bkw777/NODE_DATAPAC/PCB/out/MiniNDP_1M_B.bottom.jpg

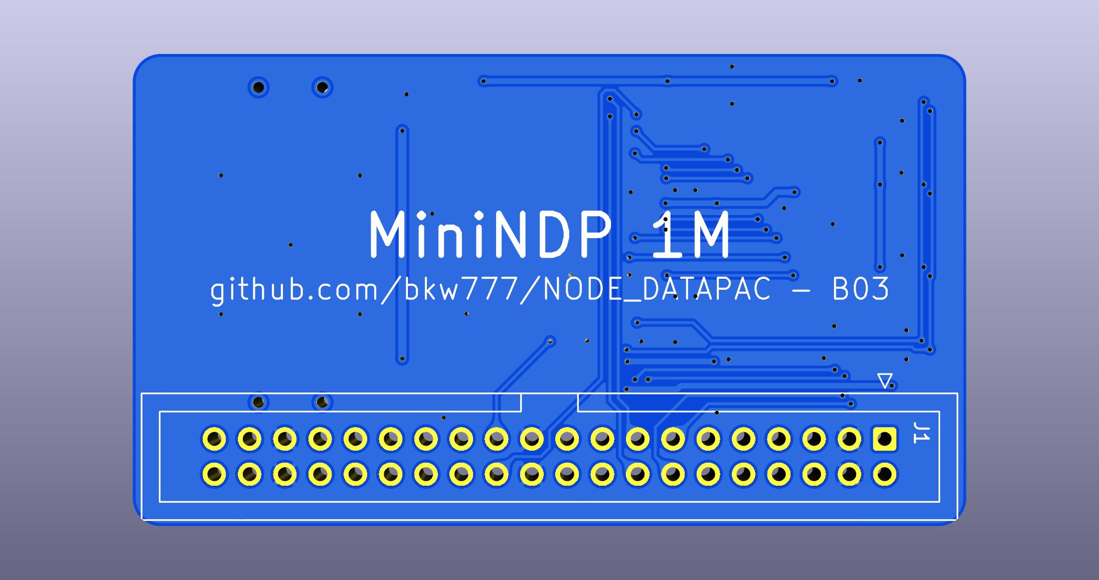
PCB/out/MiniNDP_1M_B.bottom.jpg
