bkw777/NODE_DATAPAC/PCB/out/MiniNDP_1M_B.top.jpg

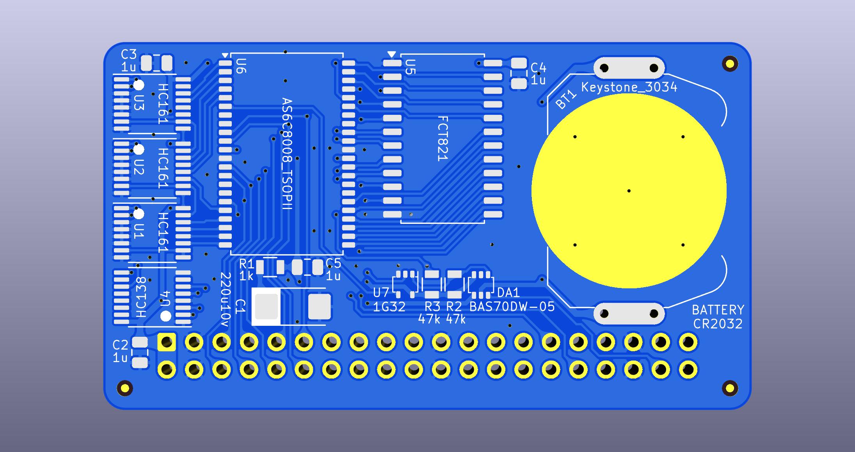
PCB/out/MiniNDP_1M_B.top.jpg
