bkw777/NODE_DATAPAC/PCB/out/MiniNDP_256_CR2016.jpg

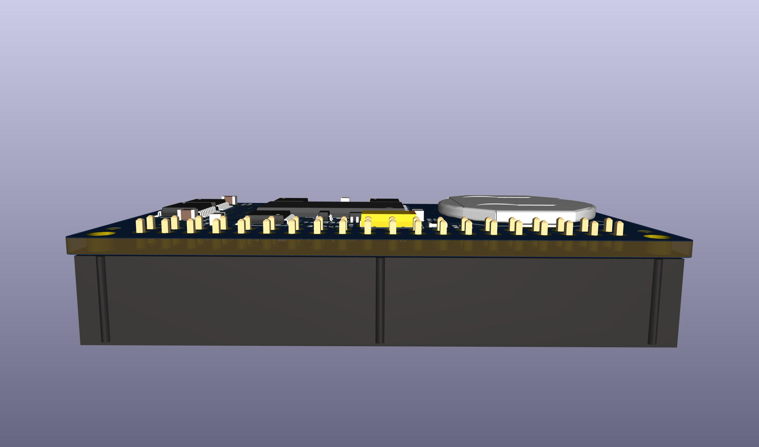
PCB/out/MiniNDP_256_CR2016.jpg
