bkw777/NODE_DATAPAC/PCB/out/MiniNDP_OG.bottom.jpg

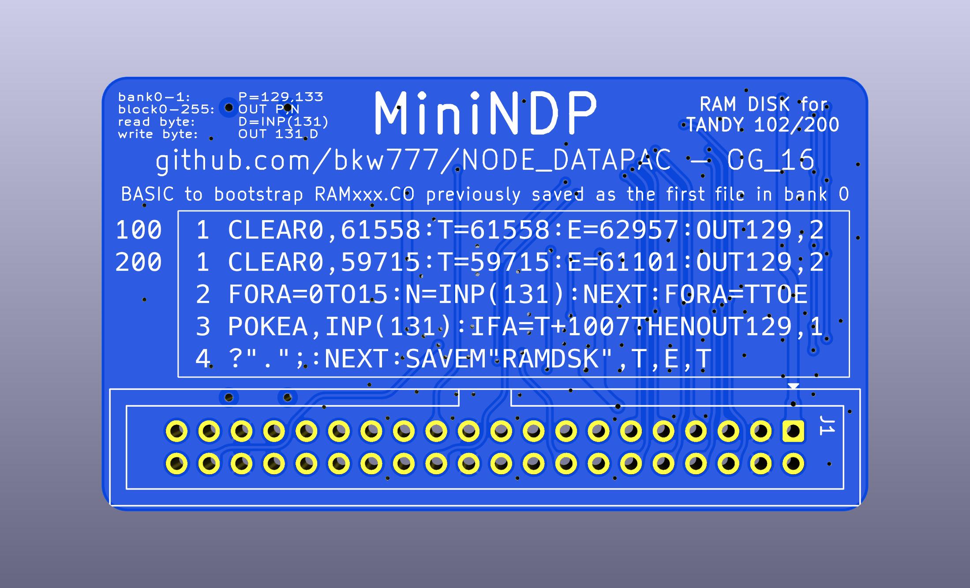
PCB/out/MiniNDP_OG.bottom.jpg
