bkw777/NODE_DATAPAC/PCB/out/MiniNDP_OG.jpg

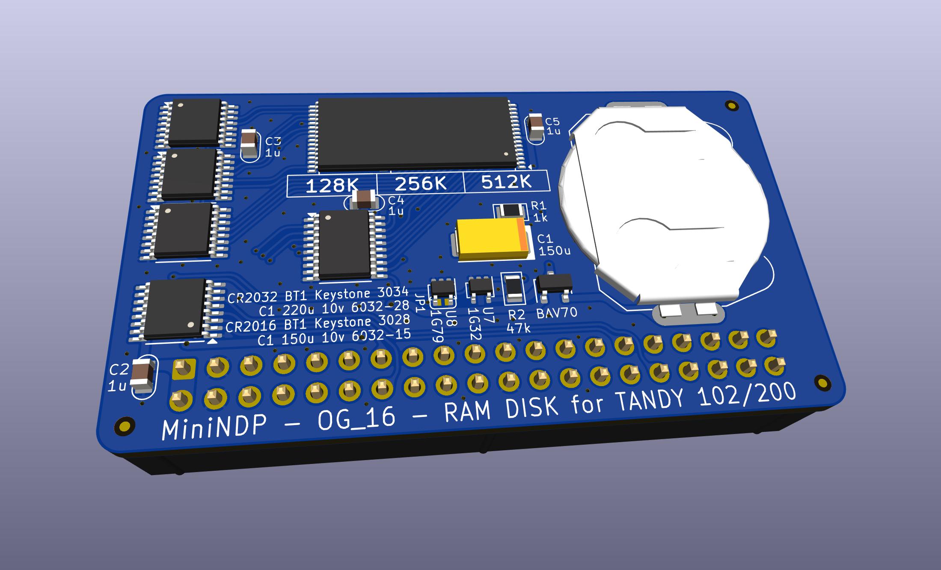
PCB/out/MiniNDP_OG.jpg
