bkw777/NODE_DATAPAC/PCB/out/MiniNDP_OG.top.jpg

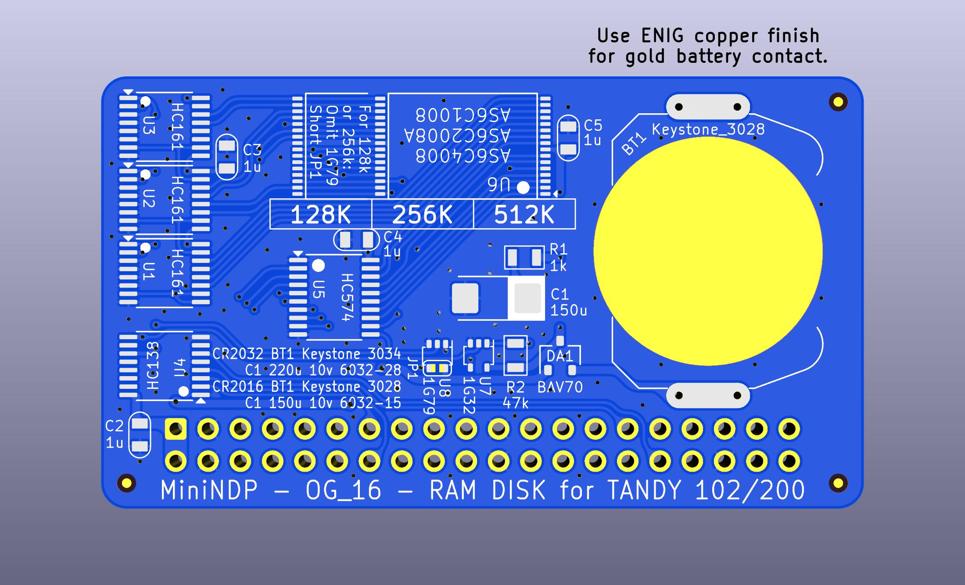
PCB/out/MiniNDP_OG.top.jpg
