bkw777/NODE_DATAPAC/PCB/out/NODE_DATAPAC_256K_bkw.bottom.jpg

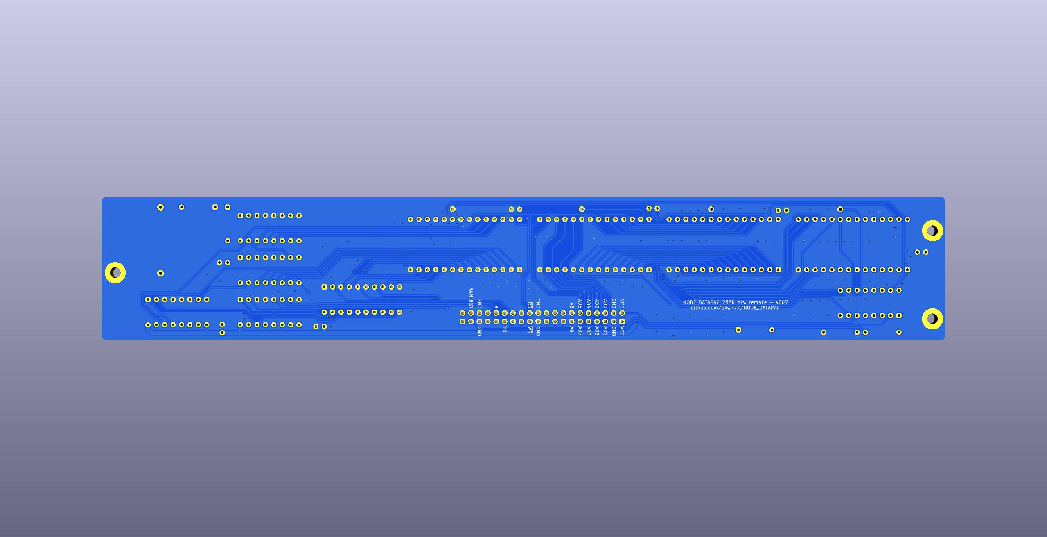
PCB/out/NODE_DATAPAC_256K_bkw.bottom.jpg
