bkw777/NODE_DATAPAC/PCB/out/NODE_DATAPAC_256K_bkw.f.jpg

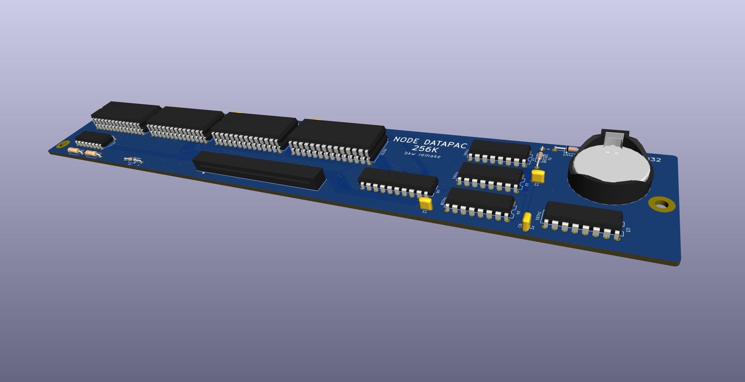
PCB/out/NODE_DATAPAC_256K_bkw.f.jpg
