bkw777/NODE_DATAPAC/PCB/out/NODE_DATAPAC_256K_historical_reproduction_2.jpg

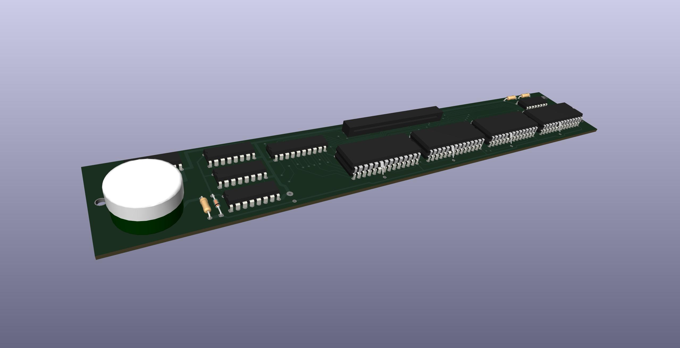
PCB/out/NODE_DATAPAC_256K_historical_reproduction_2.jpg
