bkw777/NODE_DATAPAC/PICS/cover_1.jpg

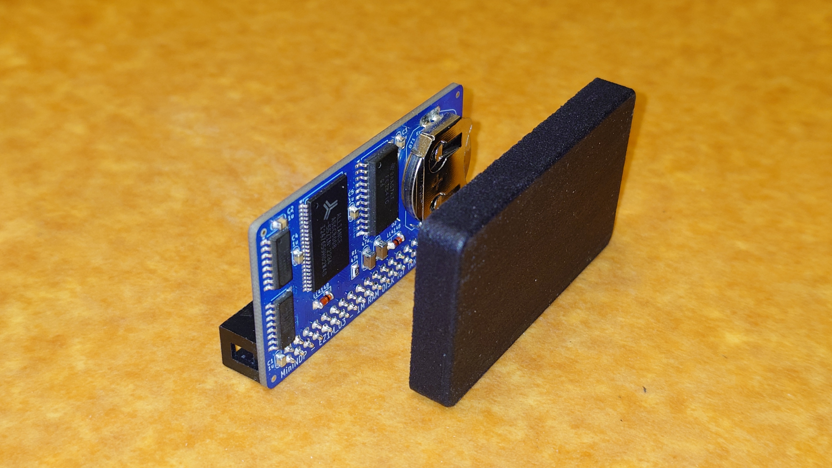
PICS/cover_1.jpg
