bkw777/NODE_DATAPAC/PICS/cover_2.jpg

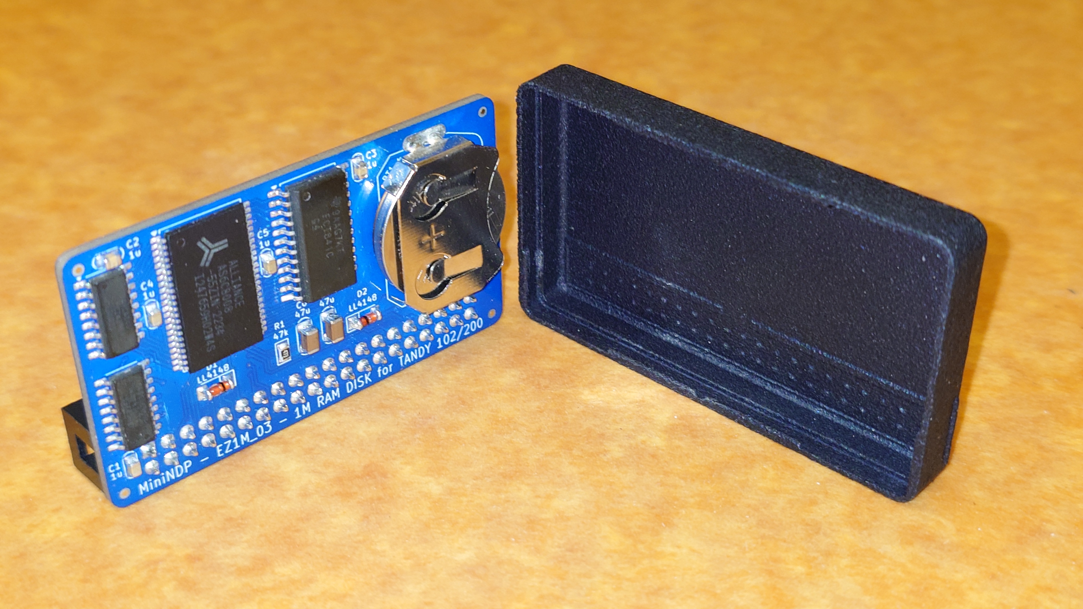
PICS/cover_2.jpg
