bkw777/NODE_DATAPAC/PICS/cover_3.jpg

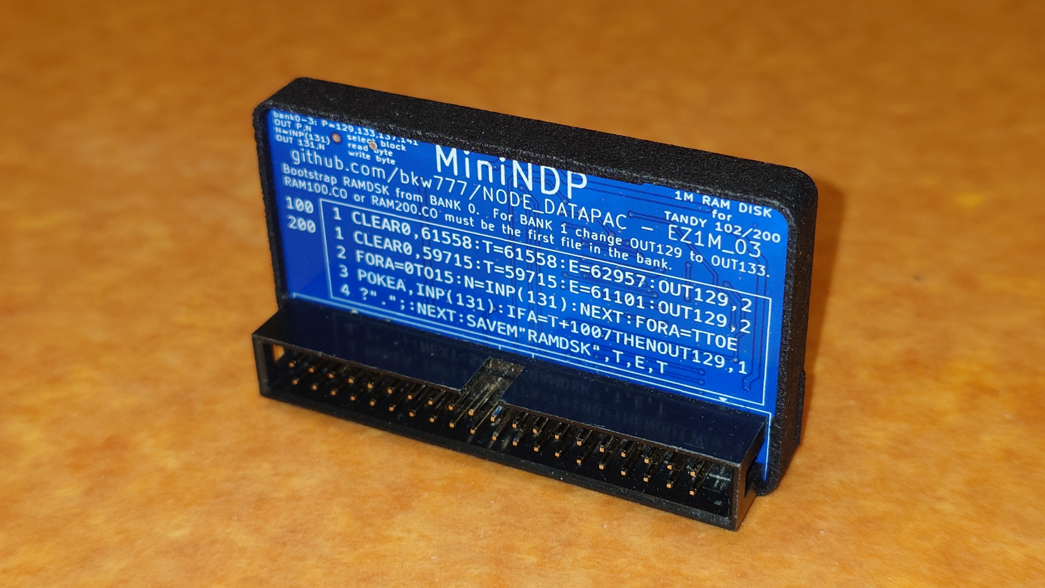
PICS/cover_3.jpg
