bkw777/NODE_DATAPAC/PICS/cover_102.jpg

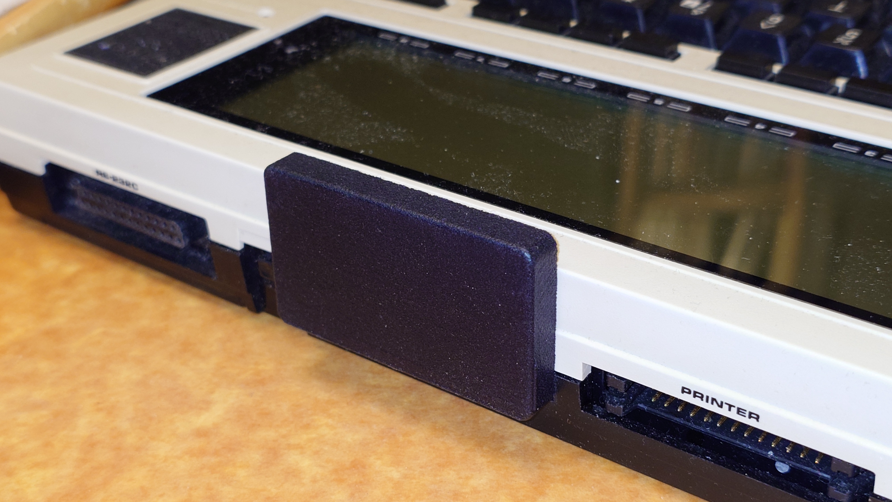
PICS/cover_102.jpg
