bkw777/NODE_DATAPAC/PICS/cover_200.jpg

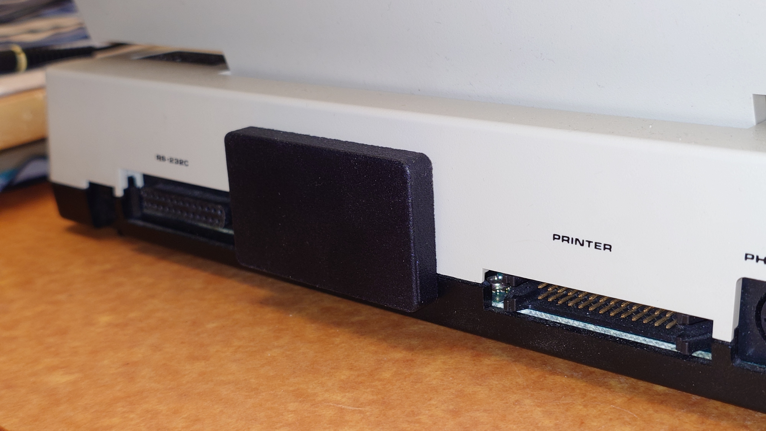
PICS/cover_200.jpg
