bkw777/NODE_DATAPAC/PICS/Cover_thin.1.jpg

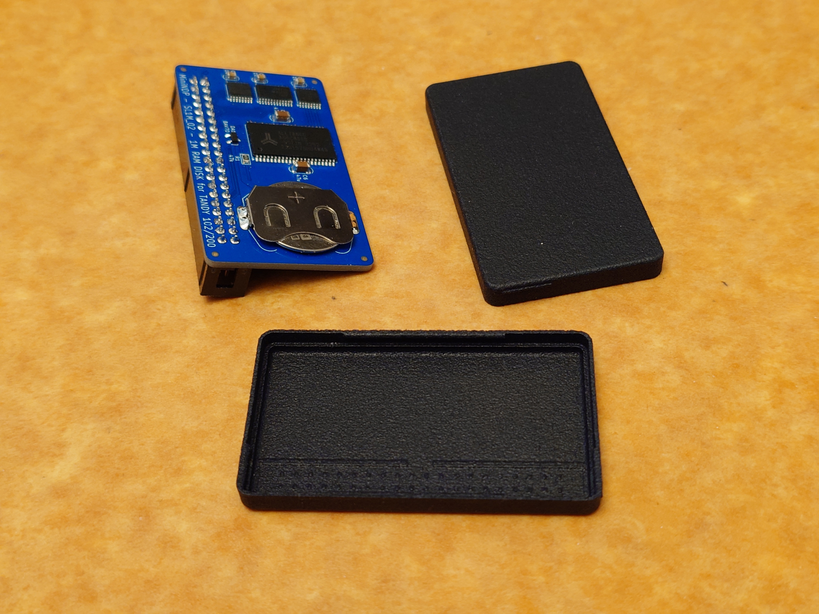
PICS/Cover_thin.1.jpg
