bkw777/NODE_DATAPAC/PICS/Cover_thin.2.jpg

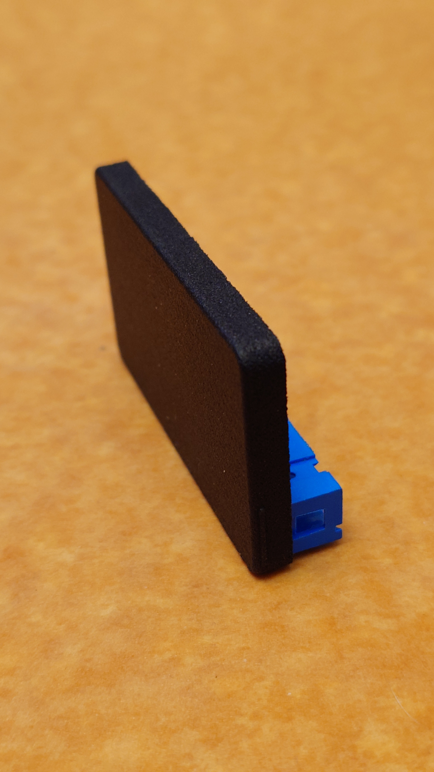
PICS/Cover_thin.2.jpg
