bkw777/NODE_DATAPAC/PICS/DATAPAC/549330443_10163459711251760_8373819885439464849_n.jpg

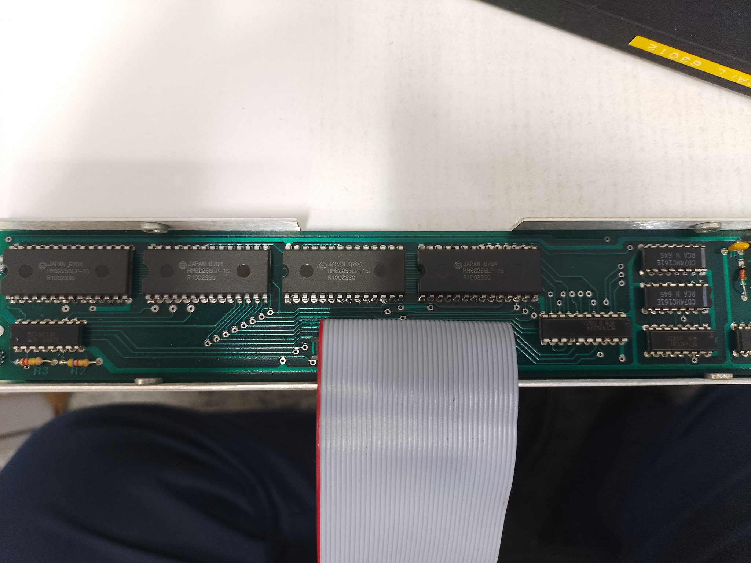
PICS/DATAPAC/549330443_10163459711251760_8373819885439464849_n.jpg
