bkw777/NODE_DATAPAC/PICS/DATAPAC/552761636_10163459711391760_1145795438437594282_n.jpg

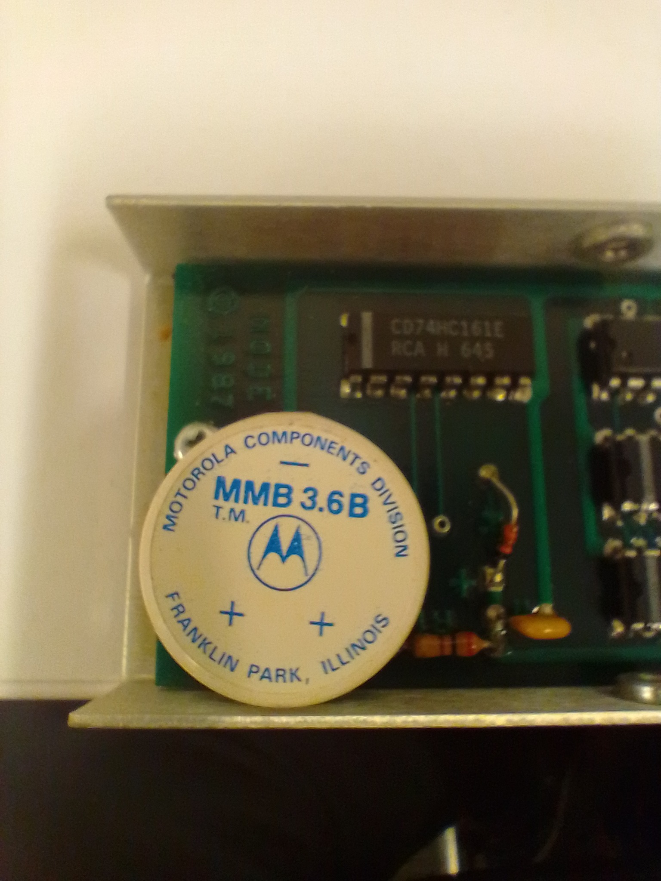
PICS/DATAPAC/552761636_10163459711391760_1145795438437594282_n.jpg
