bkw777/NODE_DATAPAC/PICS/DATAPAC/553972267_10163459710006760_2879506041436889275_n.jpg

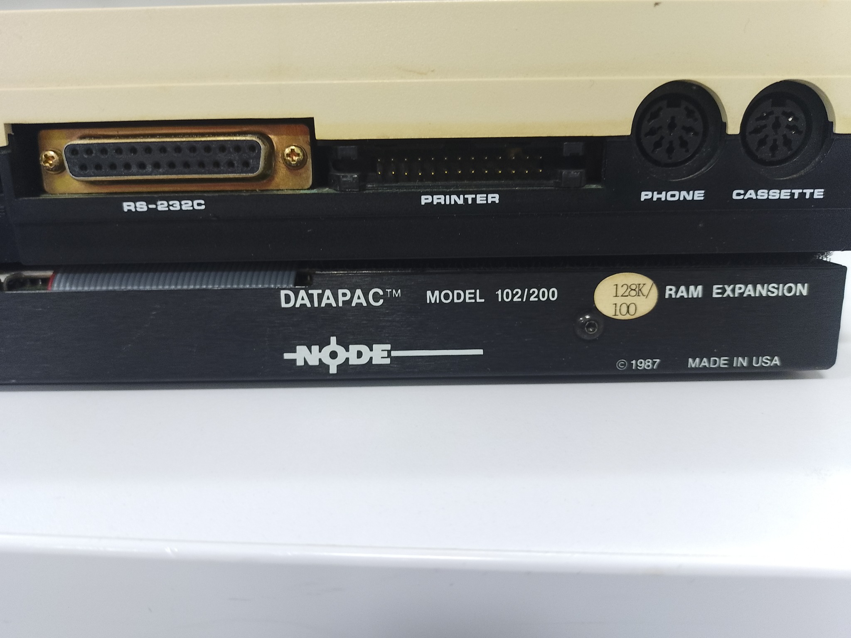
PICS/DATAPAC/553972267_10163459710006760_2879506041436889275_n.jpg
