bkw777/NODE_DATAPAC/PICS/DATAPAC/bottom.jpg

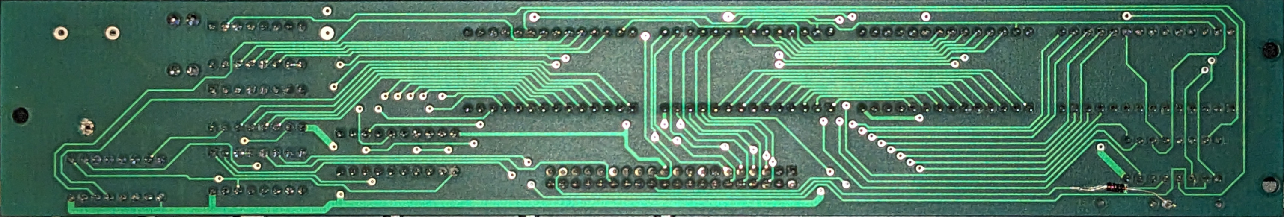
PICS/DATAPAC/bottom.jpg
