bkw777/NODE_DATAPAC/PICS/DATAPAC/D2_RAM_RST_bodge.jpg

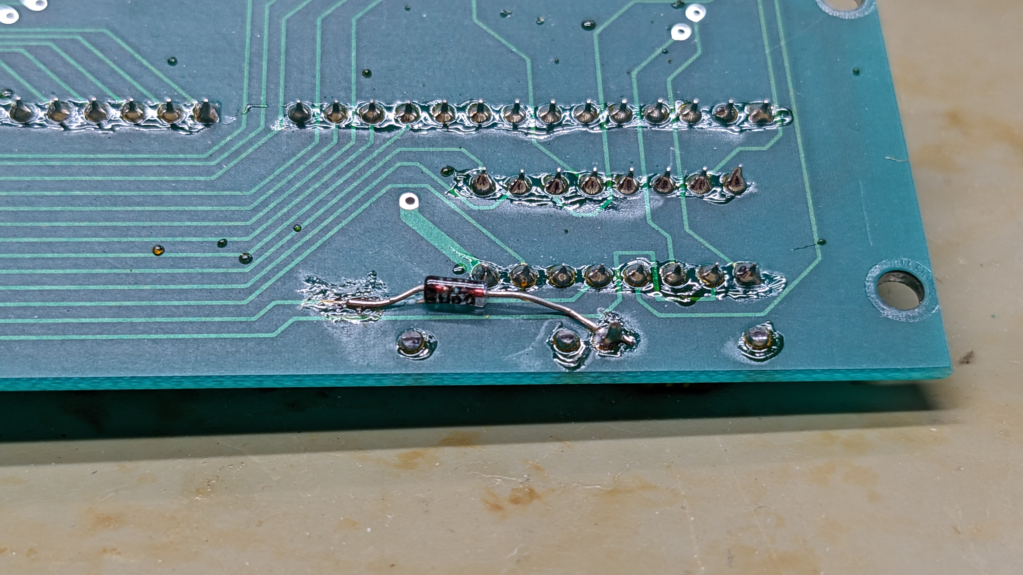
PICS/DATAPAC/D2_RAM_RST_bodge.jpg
