bkw777/NODE_DATAPAC/PICS/DATAPAC/new_battery_placement.jpg

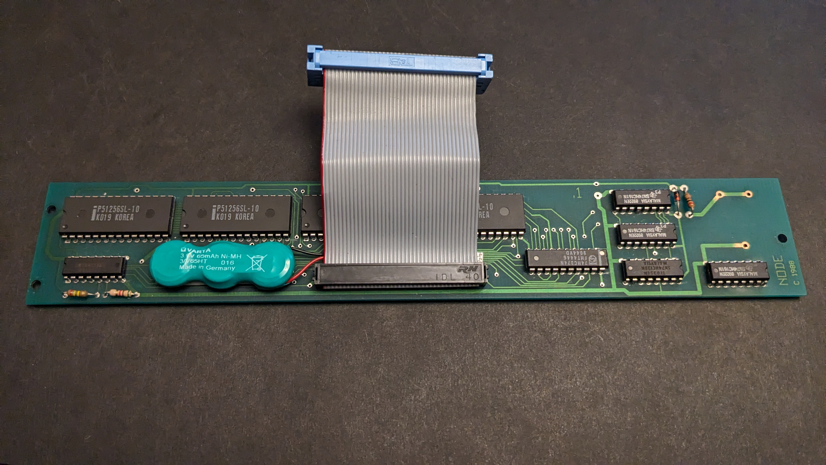
PICS/DATAPAC/new_battery_placement.jpg
