bkw777/NODE_DATAPAC/PICS/DATAPAC/part_numbers_1.jpg

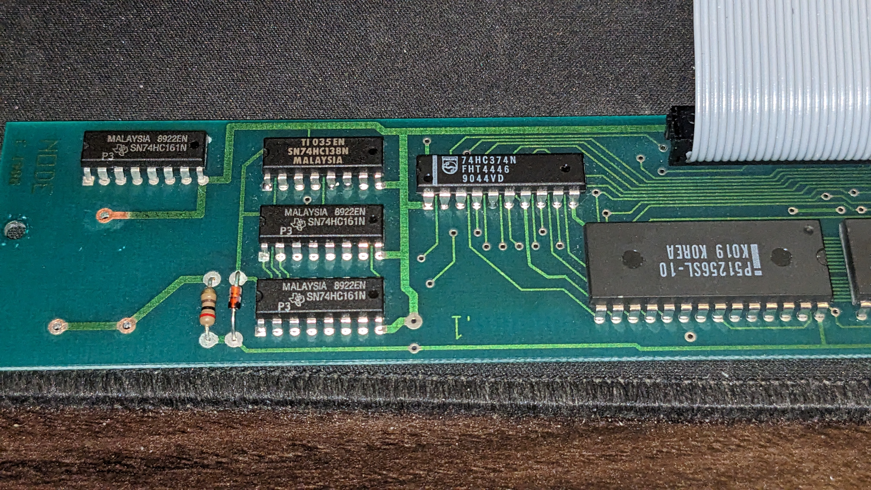
PICS/DATAPAC/part_numbers_1.jpg
