bkw777/NODE_DATAPAC/PICS/DATAPAC/part_numbers_2.jpg

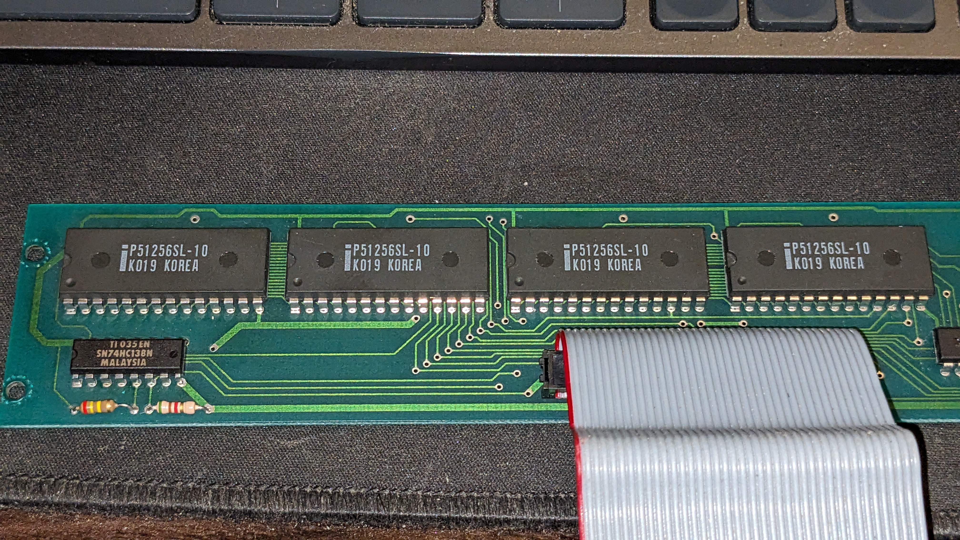
PICS/DATAPAC/part_numbers_2.jpg
