bkw777/NODE_DATAPAC/PICS/DATAPAC/PXL_20230813_234301294.jpg

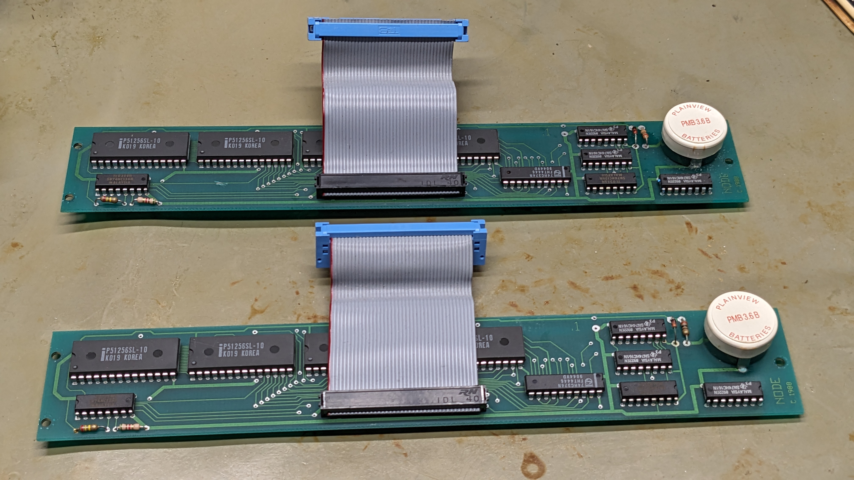
PICS/DATAPAC/PXL_20230813_234301294.jpg
