bkw777/NODE_DATAPAC/PICS/DATAPAC/PXL_20230909_004526104.jpg

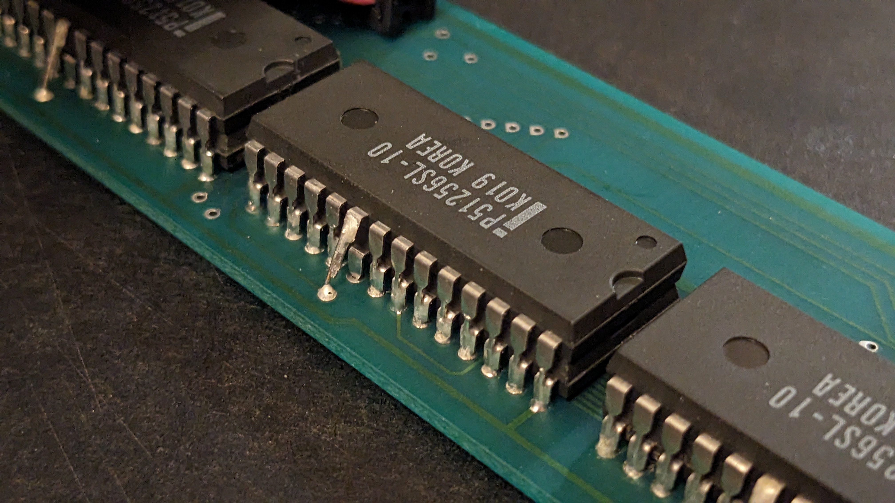
PICS/DATAPAC/PXL_20230909_004526104.jpg
