bkw777/NODE_DATAPAC/PICS/DATAPAC/PXL_20230909_004637694.jpg

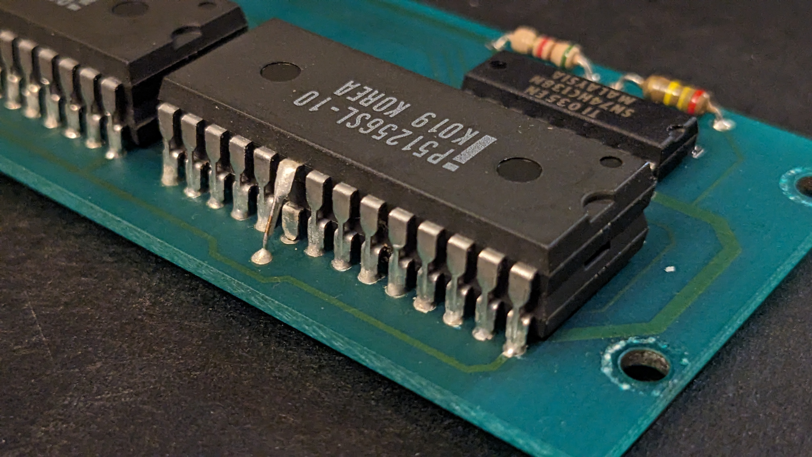
PICS/DATAPAC/PXL_20230909_004637694.jpg
