bkw777/NODE_DATAPAC/PICS/DATAPAC/top.jpg

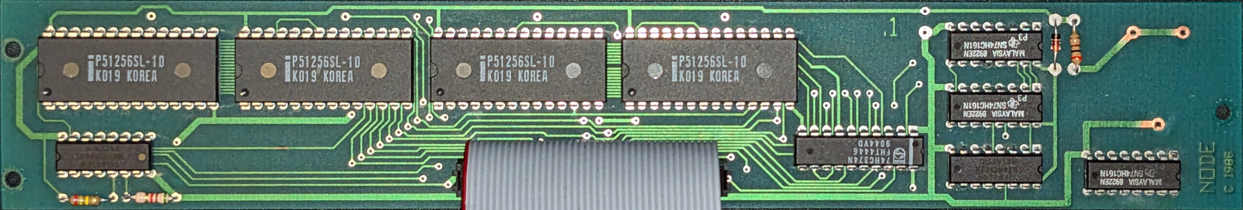
PICS/DATAPAC/top.jpg
