bkw777/NODE_DATAPAC/PICS/M10/102_200_M10_1.jpg

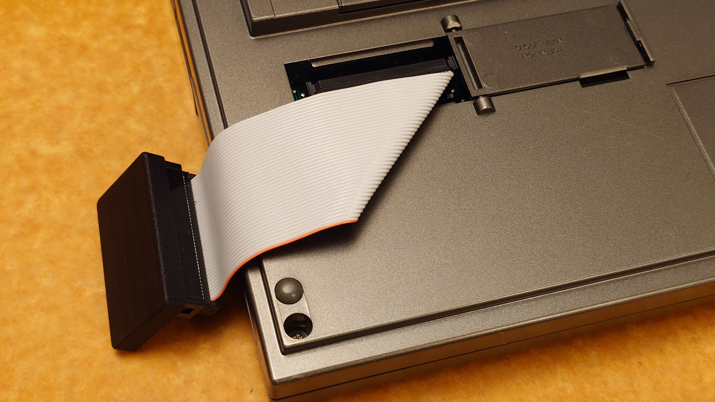
PICS/M10/102_200_M10_1.jpg
