bkw777/NODE_DATAPAC/PICS/M10/102_200_M10_2.jpg

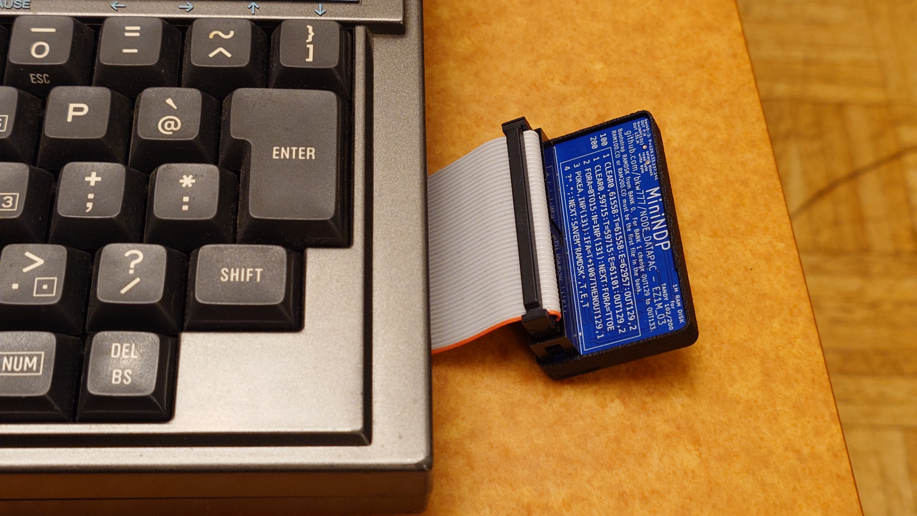
PICS/M10/102_200_M10_2.jpg
