bkw777/NODE_DATAPAC/PICS/M10/M10_1.jpg

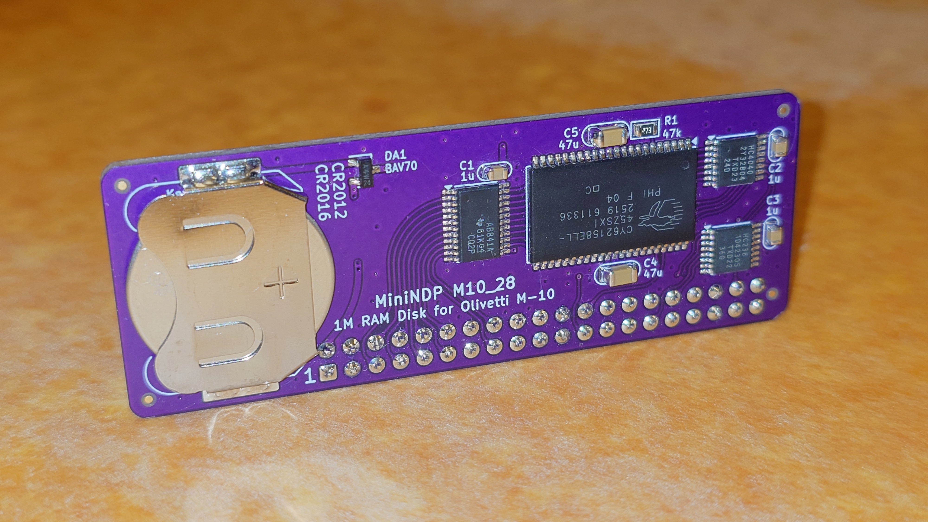
PICS/M10/M10_1.jpg
