bkw777/NODE_DATAPAC/PICS/M10/M10_2.jpg

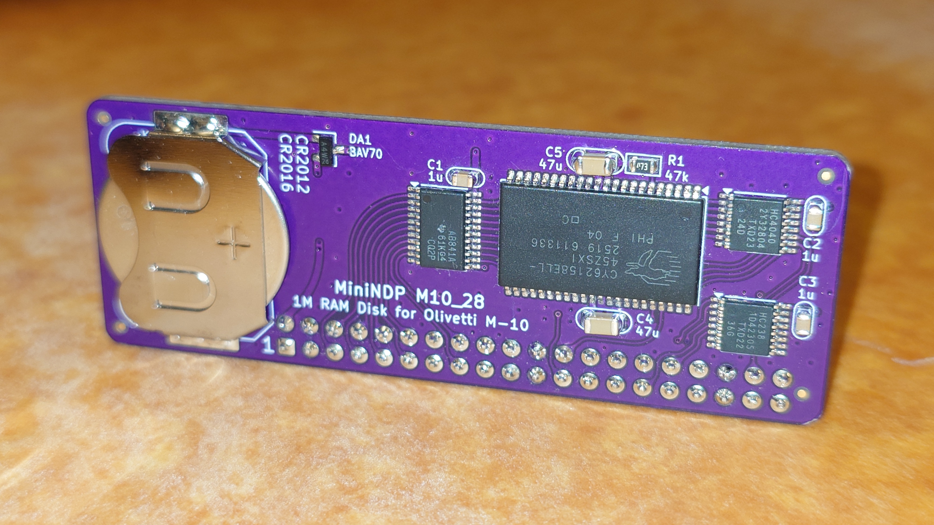
PICS/M10/M10_2.jpg
