bkw777/NODE_DATAPAC/PICS/M10/M10_3.jpg

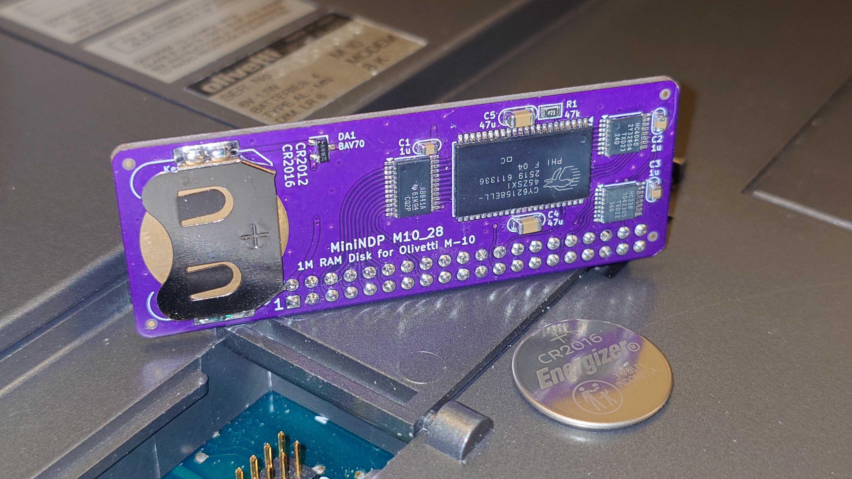
PICS/M10/M10_3.jpg
