bkw777/NODE_DATAPAC/PICS/M10/M10_back.jpg

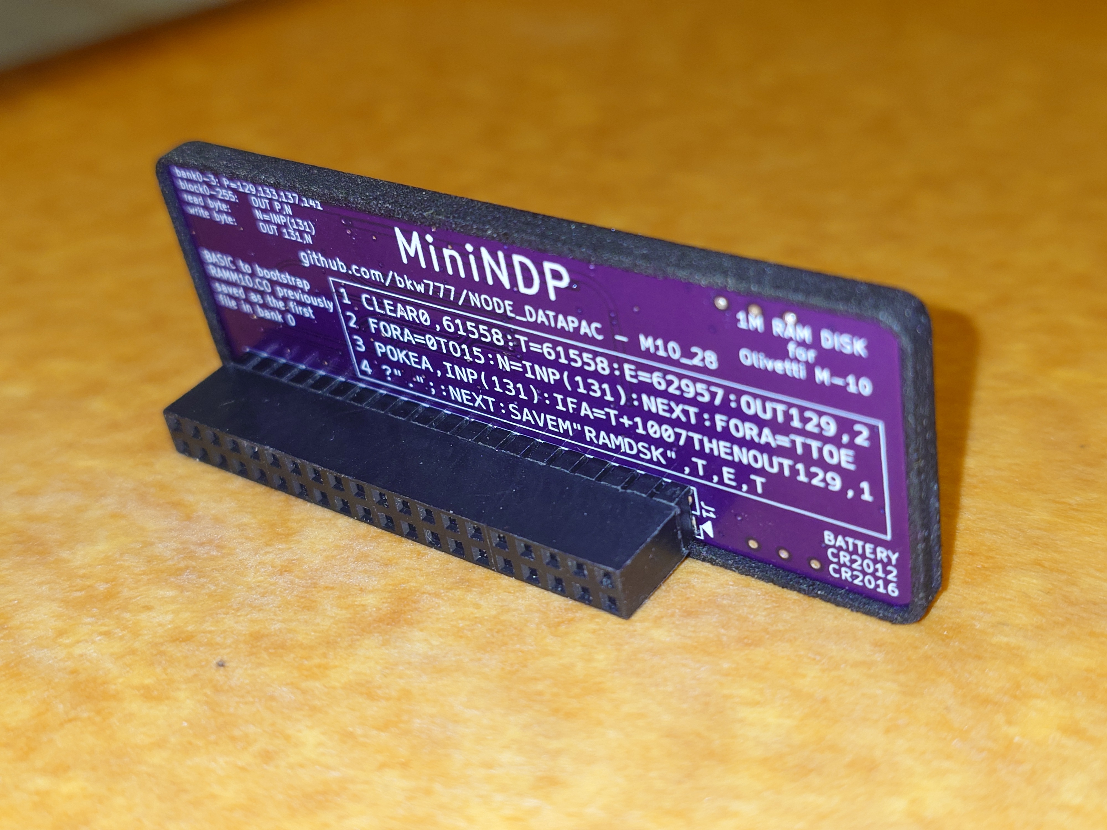
PICS/M10/M10_back.jpg
