bkw777/NODE_DATAPAC/PICS/M10/M10_battery_door_closed.jpg

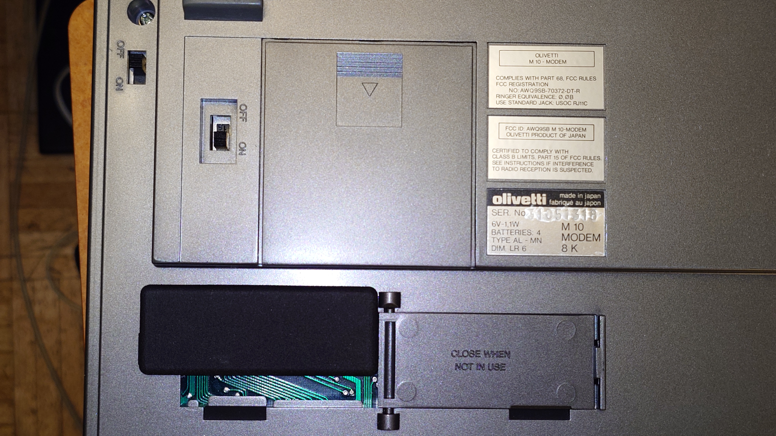
PICS/M10/M10_battery_door_closed.jpg
