bkw777/NODE_DATAPAC/PICS/M10/M10_bottom_clearance.jpg

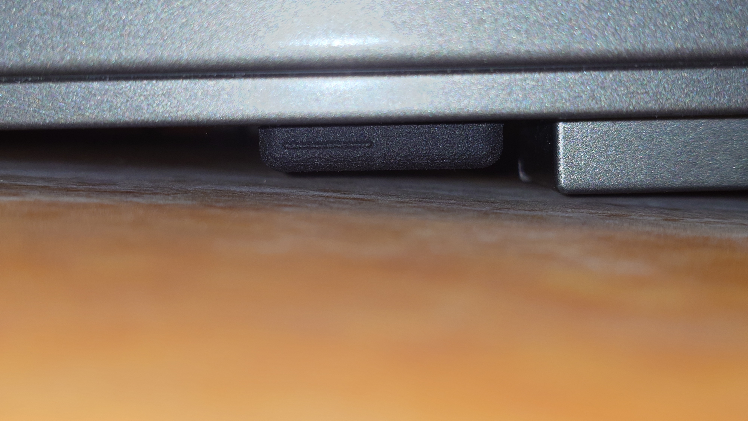
PICS/M10/M10_bottom_clearance.jpg
