bkw777/NODE_DATAPAC/PICS/rampac/20260724_151853155.JPG

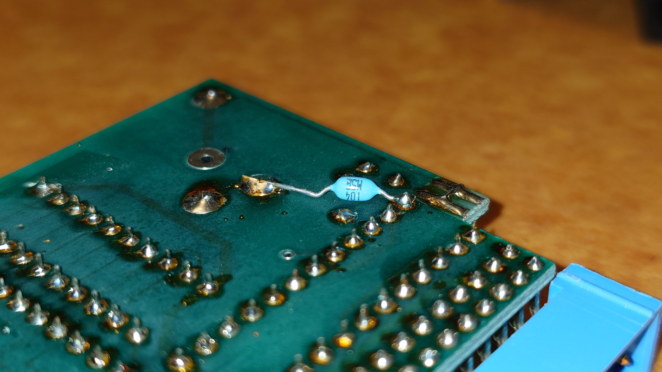
PICS/rampac/20260724_151853155.JPG
