bkw777/NODE_DATAPAC/PICS/rampac/20260724_151917631.JPG

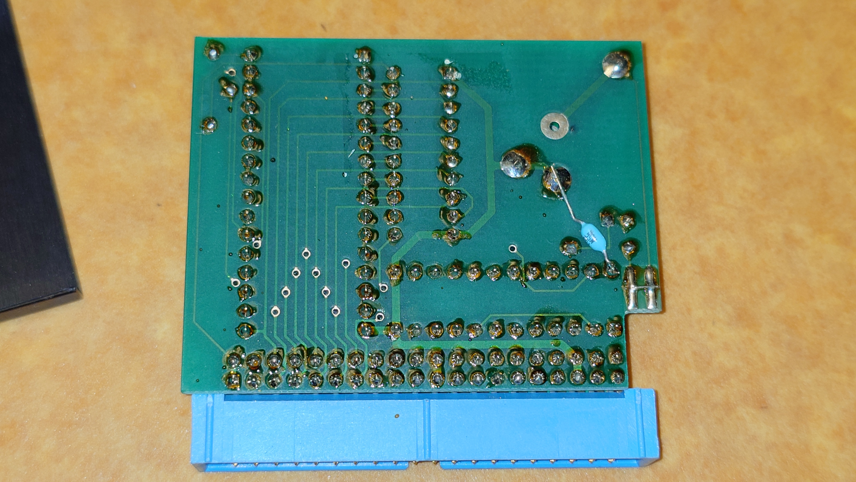
PICS/rampac/20260724_151917631.JPG
