bkw777/NODE_DATAPAC/PICS/rampac/20260724_151938833.JPG

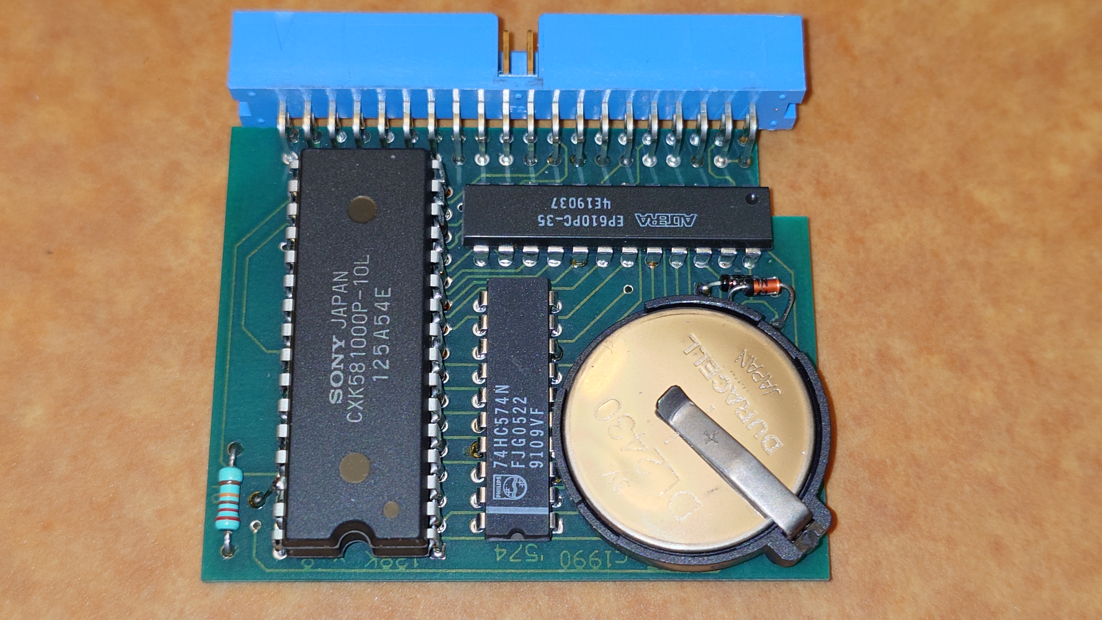
PICS/rampac/20260724_151938833.JPG
