bkw777/NODE_DATAPAC/PICS/rampac/20260724_151949156.JPG

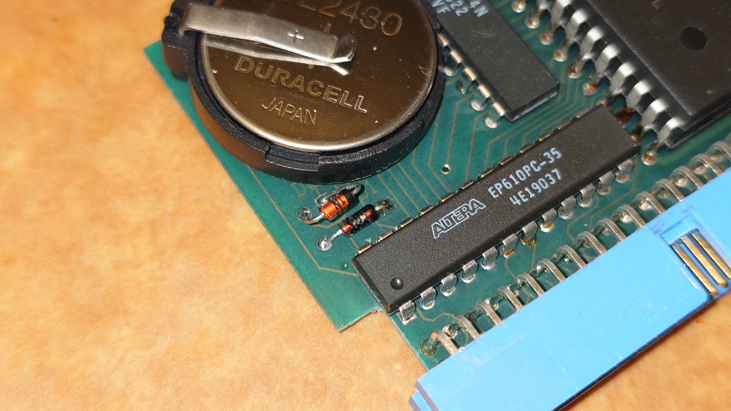
PICS/rampac/20260724_151949156.JPG
