bkw777/NODE_DATAPAC/PICS/rampac/20260724_152216495.JPG

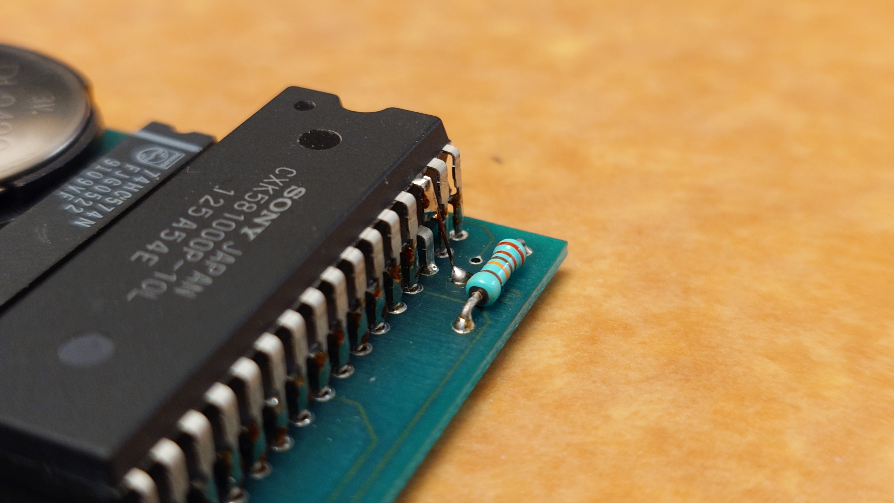
PICS/rampac/20260724_152216495.JPG
