bkw777/NODE_DATAPAC/PICS/rampac/20260724_152809876.JPG

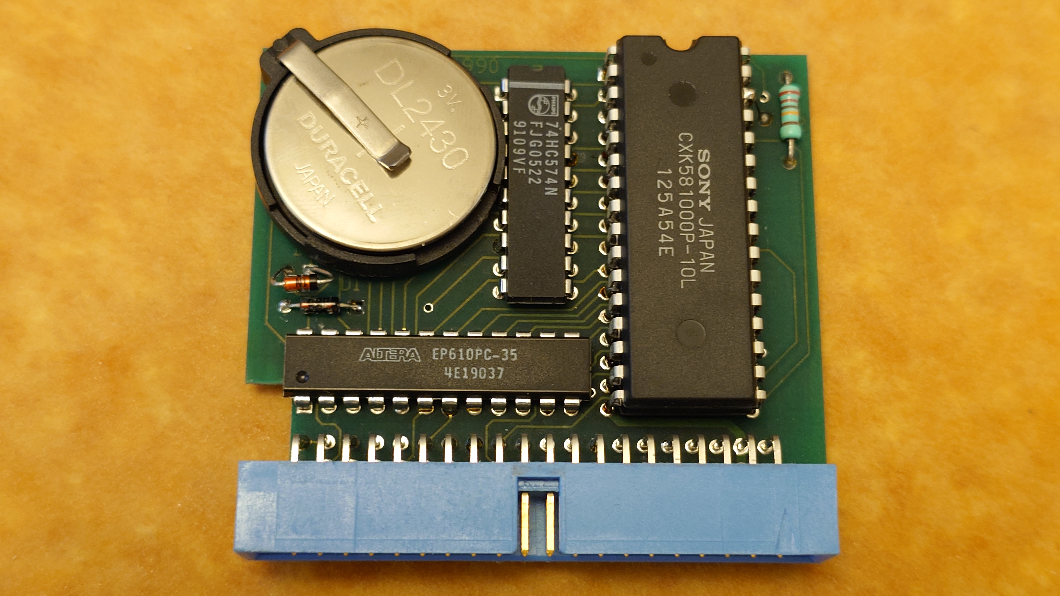
PICS/rampac/20260724_152809876.JPG
