bkw777/NODE_DATAPAC/PICS/rampac/20260724_152843507.JPG

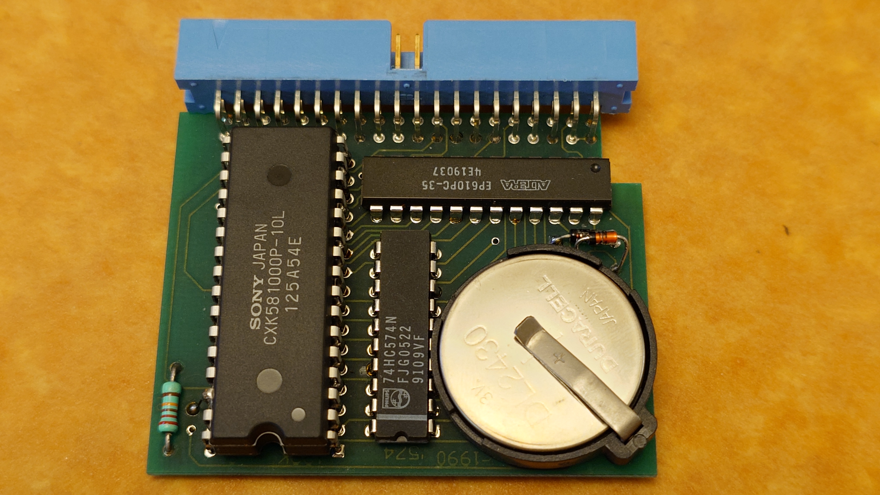
PICS/rampac/20260724_152843507.JPG
