bkw777/NODE_DATAPAC/PICS/rampac/20260724_153756693.JPG

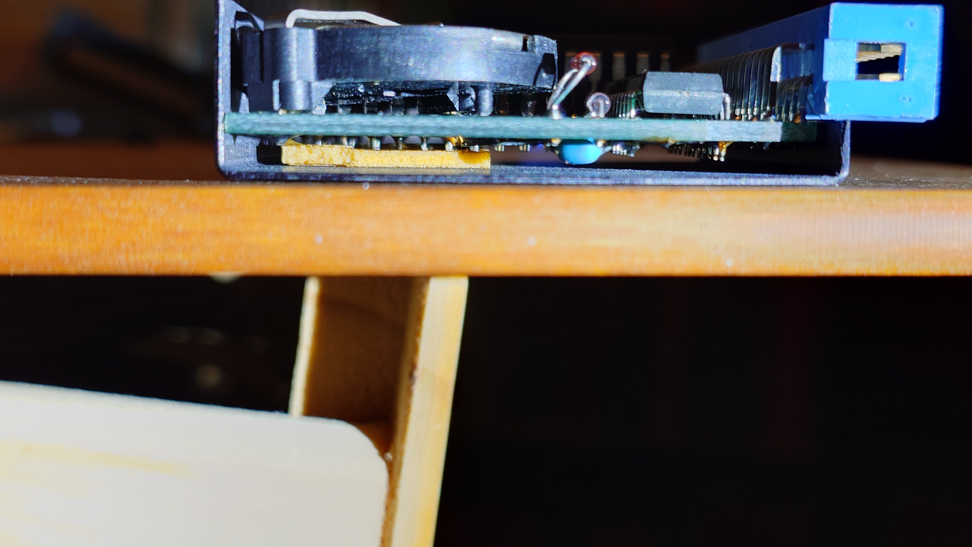
PICS/rampac/20260724_153756693.JPG
