bkw777/NODE_DATAPAC/PICS/rampac/20260724_154404858.JPG

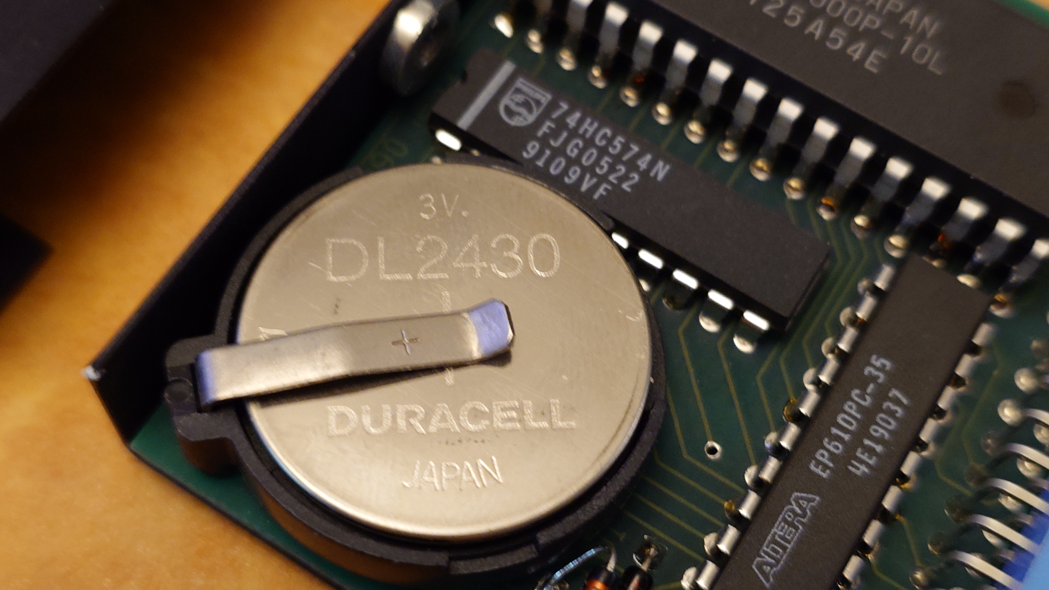
PICS/rampac/20260724_154404858.JPG
