bkw777/NODE_DATAPAC/PICS/rampac/20260724_155110646.JPG

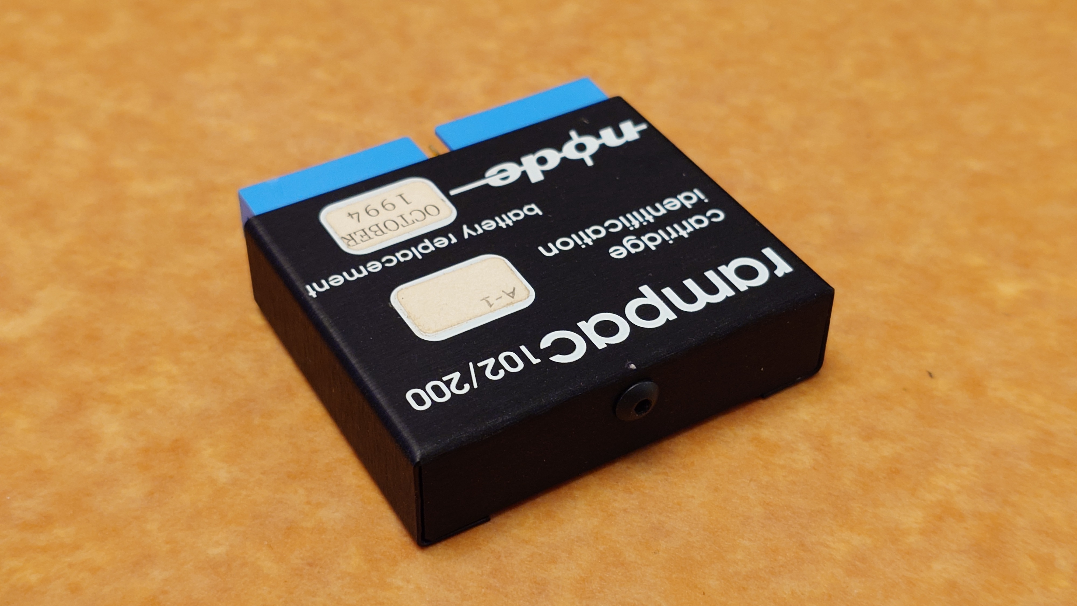
PICS/rampac/20260724_155110646.JPG
