bkw777/NODE_DATAPAC/PICS/rampac/20260724_155125823.JPG

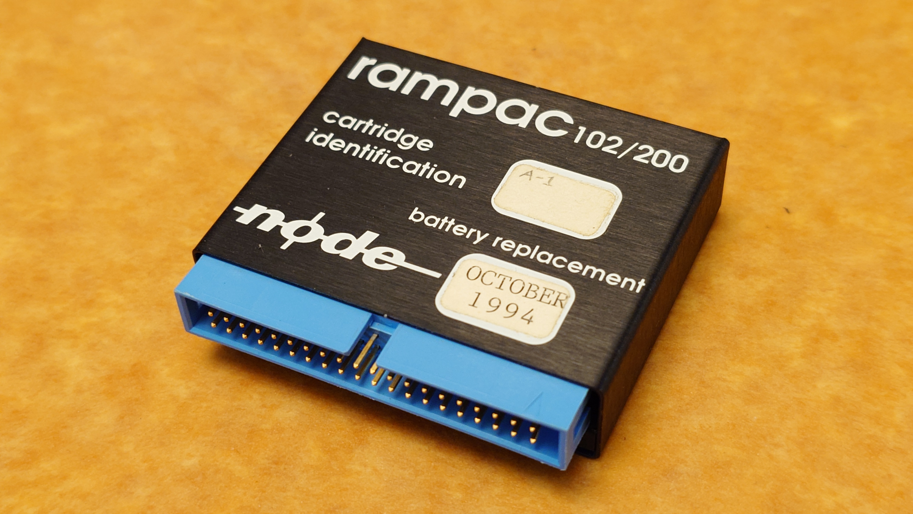
PICS/rampac/20260724_155125823.JPG
