bkw777/NODE_DATAPAC/PICS/rampac/20260724_155340259.JPG

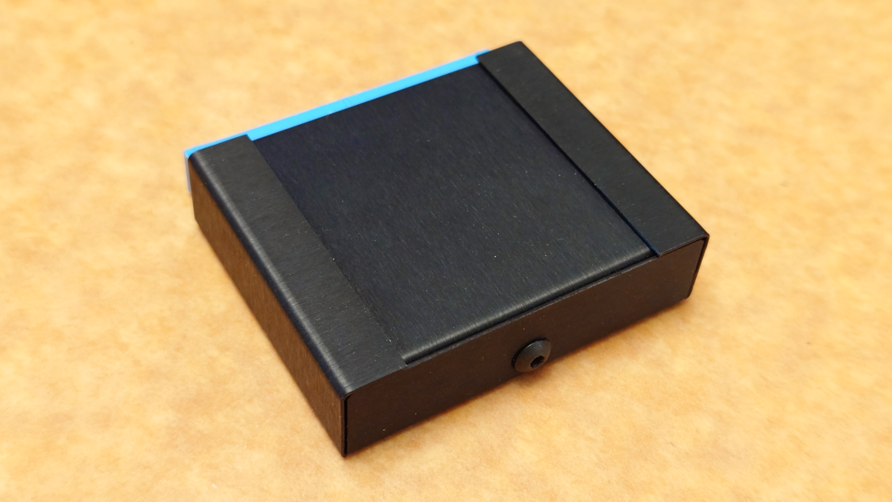
PICS/rampac/20260724_155340259.JPG
