bkw777/NODE_DATAPAC/PICS/rampac/20260724_155409336.JPG

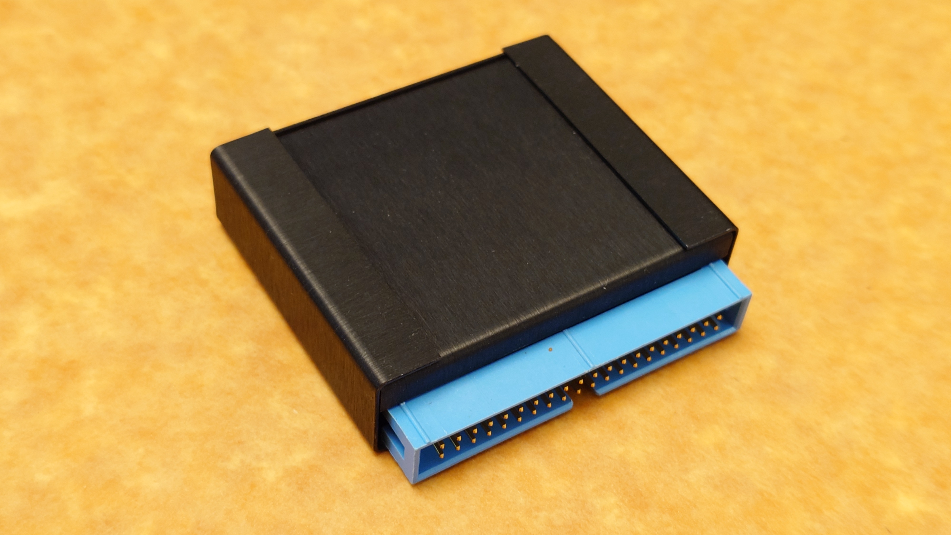
PICS/rampac/20260724_155409336.JPG
