bkw777/NODE_DATAPAC/PICS/rampac/20260724_164330944.JPG

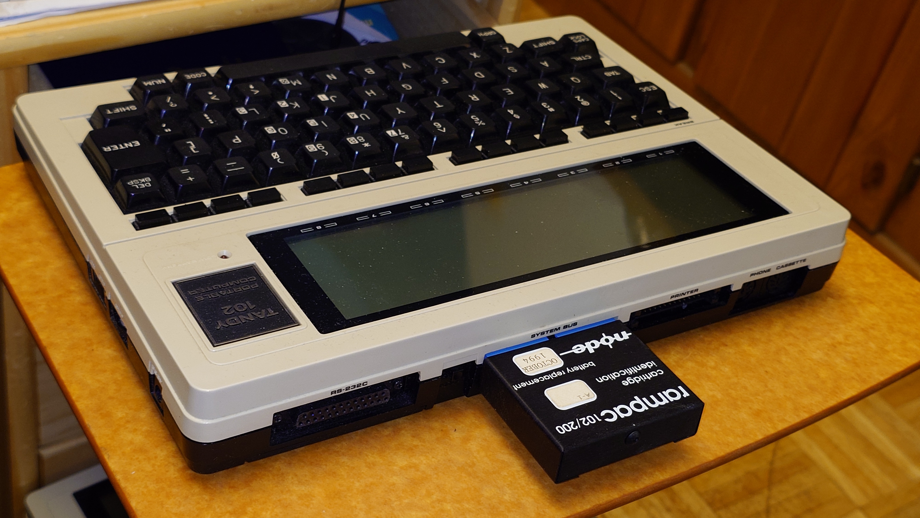
PICS/rampac/20260724_164330944.JPG
