bkw777/NODE_DATAPAC/PICS/rampac/20260724_170216820.JPG

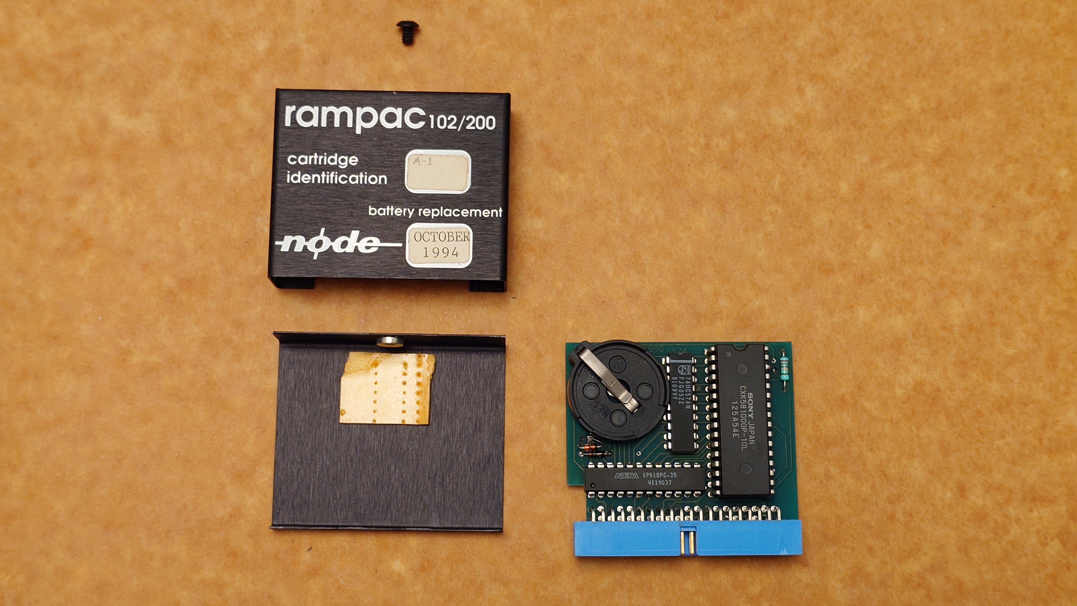
PICS/rampac/20260724_170216820.JPG
