bkw777/NODE_DATAPAC/PICS/rampac/20260724_170511586.JPG

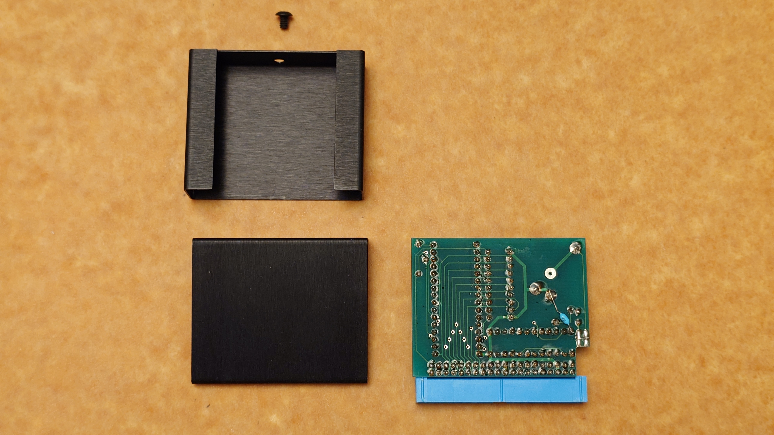
PICS/rampac/20260724_170511586.JPG
