bkw777/NODE_DATAPAC/ref/MiniNDP_and_cover.back.jpg

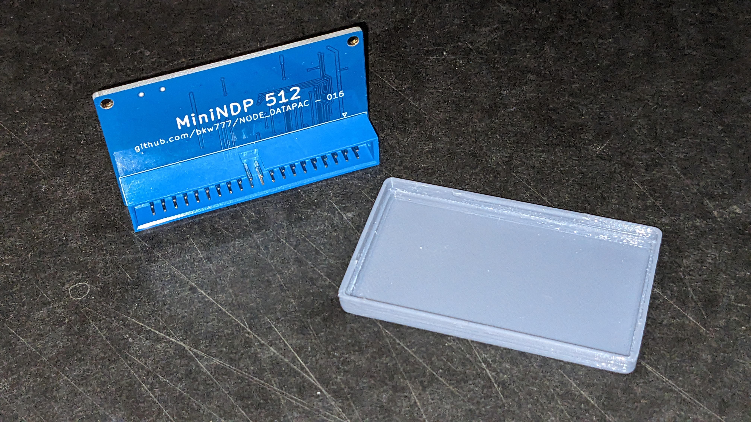
ref/MiniNDP_and_cover.back.jpg
