bkw777/NODE_DATAPAC/ref/MiniNDP_and_cover.jpg

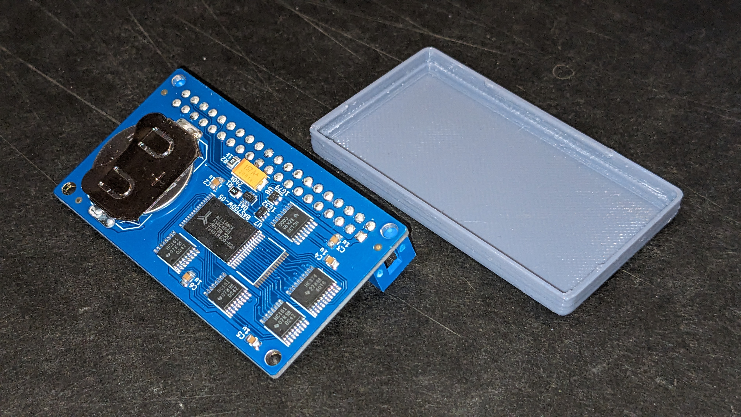
ref/MiniNDP_and_cover.jpg
