bkw777/NODE_DATAPAC/ref/MiniNDP_bank0.jpg

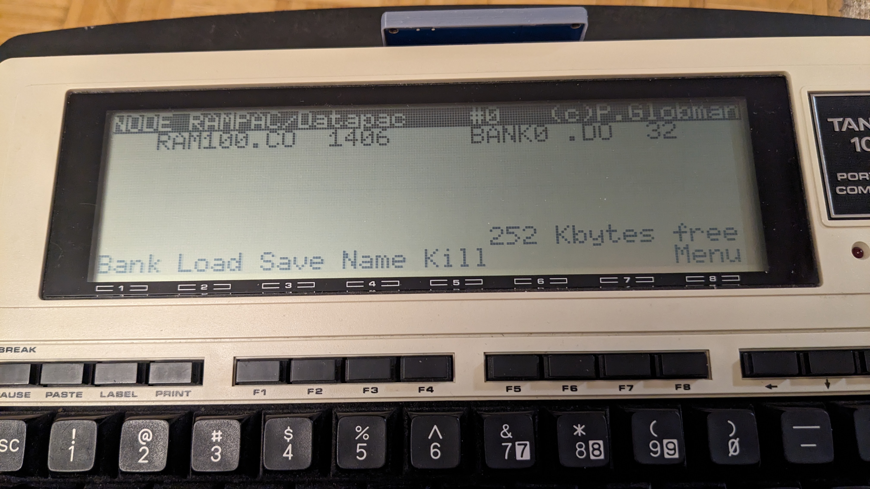
ref/MiniNDP_bank0.jpg
