bkw777/NODE_DATAPAC/ref/MiniNDP_bank1.jpg

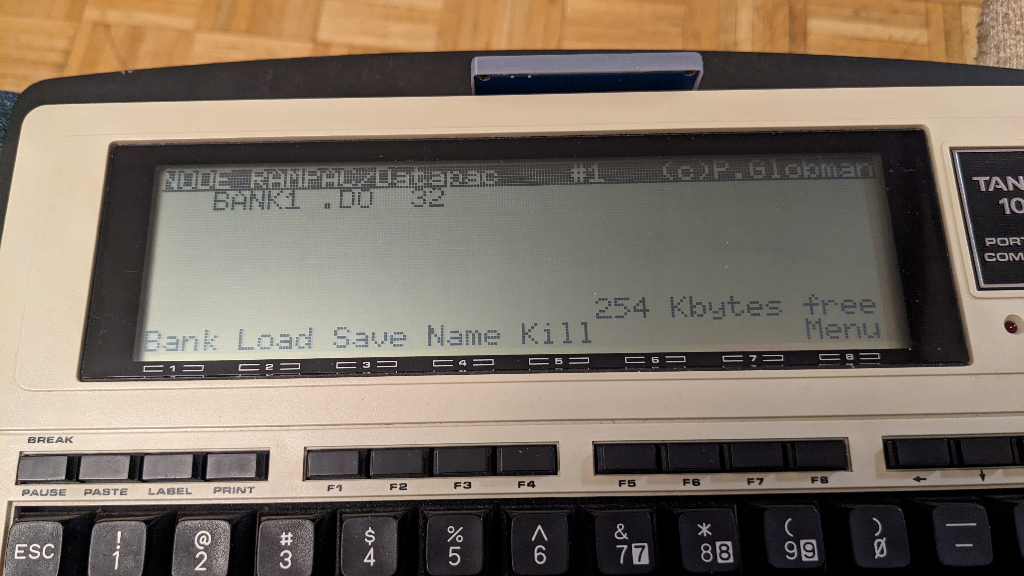
ref/MiniNDP_bank1.jpg
