bkw777/NODE_DATAPAC/ref/MiniNDP_M10_1.jpg

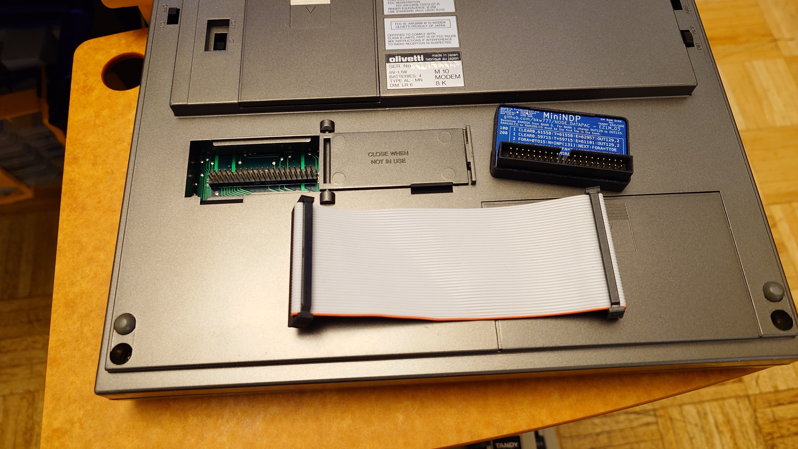
ref/MiniNDP_M10_1.jpg
