bkw777/NODE_DATAPAC/ref/MiniNDP_M10_2.jpg

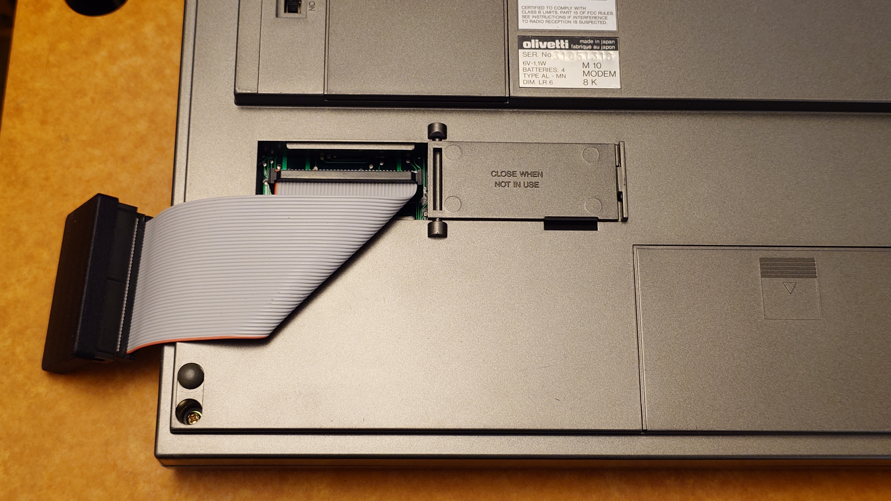
ref/MiniNDP_M10_2.jpg
