bkw777/NODE_DATAPAC/ref/MiniNDP_M10_3.jpg

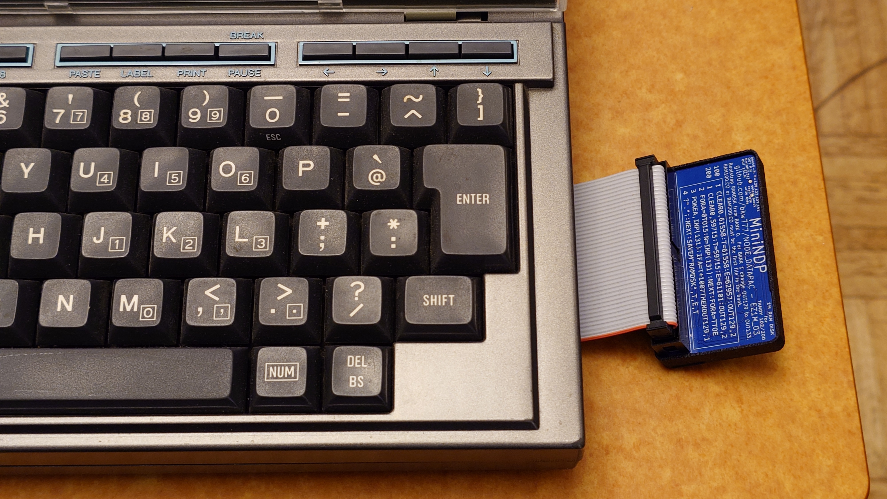
ref/MiniNDP_M10_3.jpg
