bkw777/NODE_DATAPAC/ref/MiniNDP_M10_4.jpg

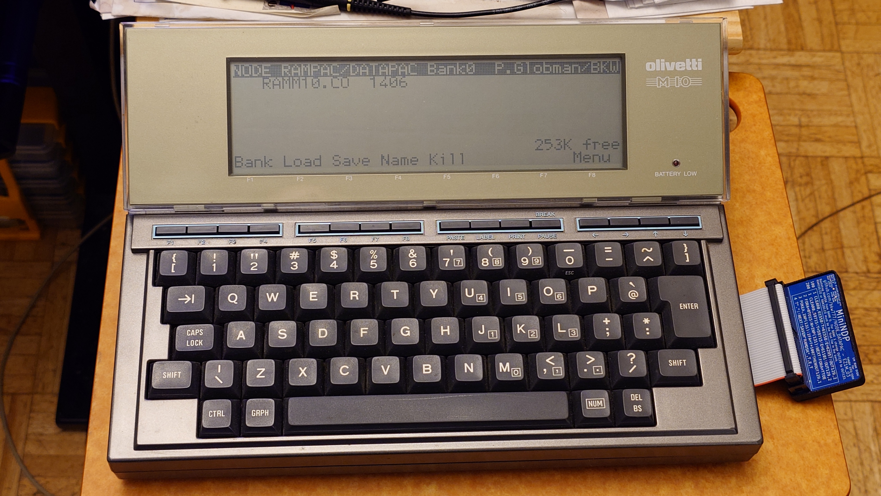
ref/MiniNDP_M10_4.jpg
