bkw777/NODE_DATAPAC/ref/T200_adapter.jpg

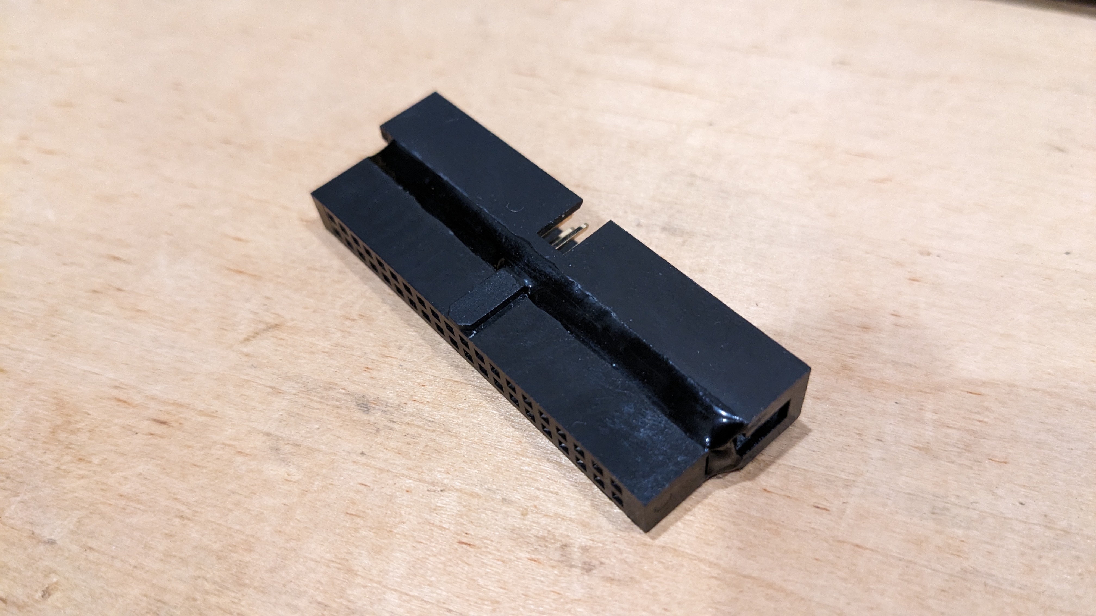
ref/T200_adapter.jpg
