bkw777/NODE_DATAPAC/PCB/NODE_DATAPAC_256K_bkw.kicad_pcb

## KiCad design PCB/NODE_DATAPAC_256K_bkw.kicad_pcb (2024-11-30)

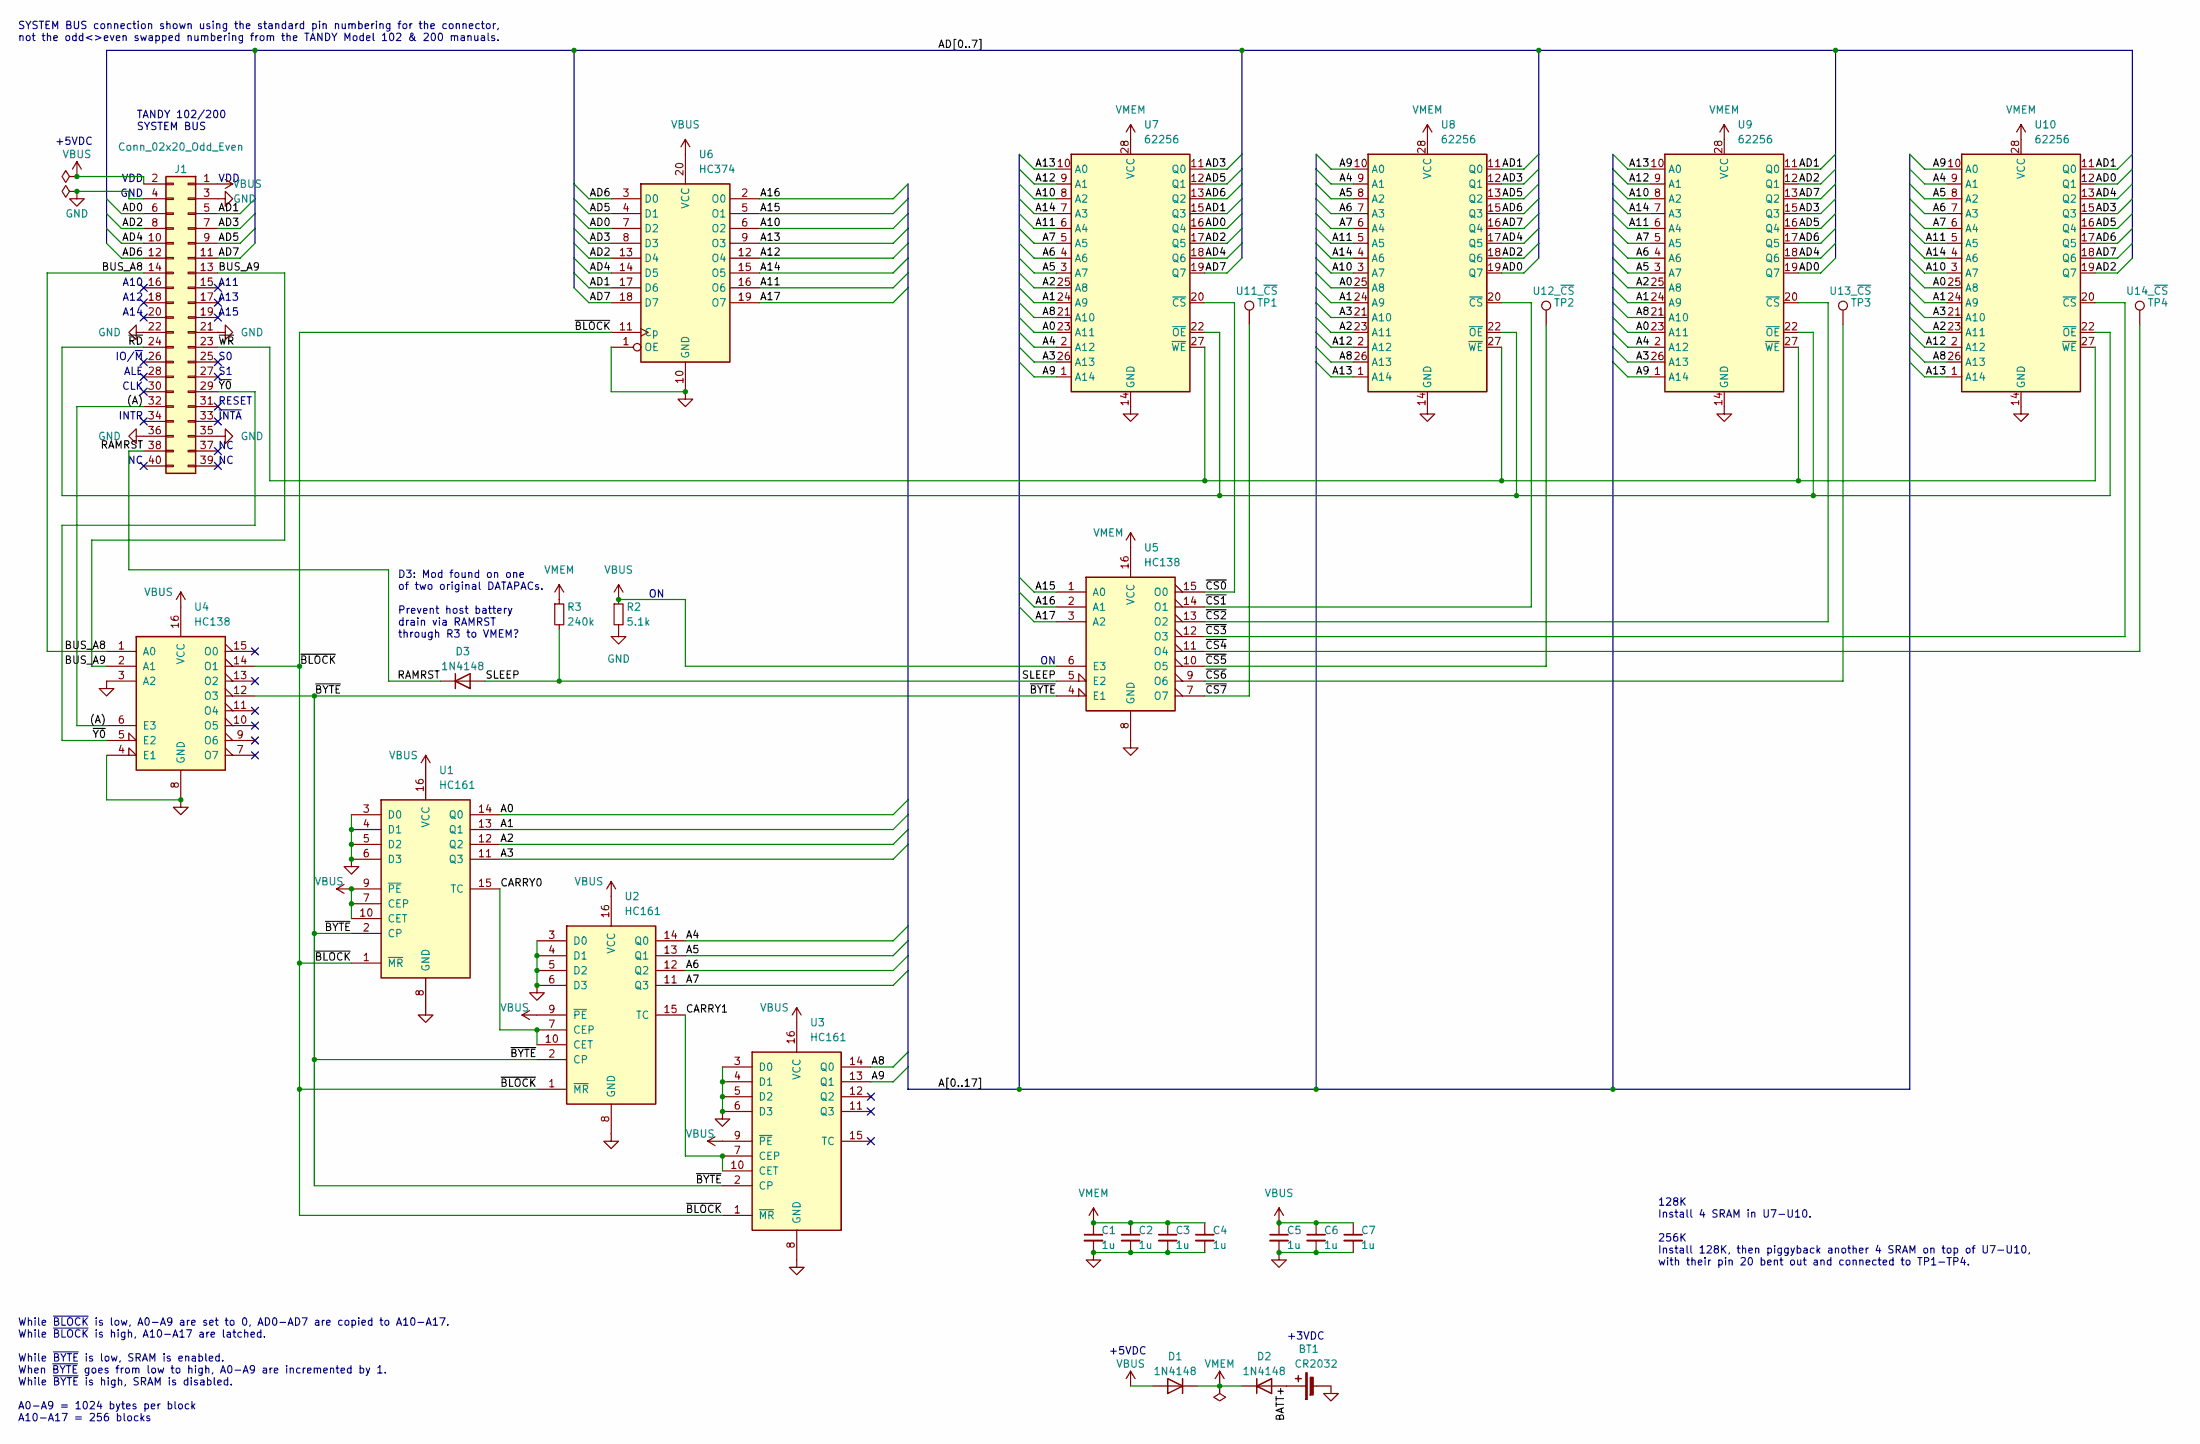
[picture p150: schematic NODE_DATAPAC_256K_bkw.kicad_sch, NODE DATAPAC 256K bkw]

Parts:
BT1: CR2032; BH-25x-x
C1, C2, C3, C4, C5, C6, C7: 1u; C_cer_tht_p2.5
D1, D2, D3: 1N4148; D_DO-35_SOD27_P10.16mm_Horizontal
J1: Conn_02x20_Odd_Even; IDC_to_board_2x20
R2: 5.1k; R_Axial_DIN0207_L6.3mm_D2.5mm_P10.16mm_Horizontal
R3: 240k; R_Axial_DIN0207_L6.3mm_D2.5mm_P10.16mm_Horizontal
TP1: U11_~{CS}; TP_THT
TP2: U12_~{CS}; TP_THT
TP3: U13_~{CS}; TP_THT
TP4: U14_~{CS}; TP_THT
U1, U2, U3: HC161; DIP-16_W7.62mm
U4, U5: HC138; DIP-16_W7.62mm
U6: HC374; DIP-20_W7.62mm
U7, U8, U9, U10: 62256; DIP-28_W15.24mm

Connections:
/(A): J1.32, U4.6 (E3)
/A0: U1.14 (Q0), U7.23 (A11), U8.25 (A8), U9.23 (A11), U10.25 (A8)
/A1: U1.13 (Q1), U7.24 (A9), U8.24 (A9), U9.24 (A9), U10.24 (A9)
/A2: U1.12 (Q2), U7.25 (A8), U8.23 (A11), U9.25 (A8), U10.23 (A11)
/A3: U1.11 (Q3), U7.26 (A13), U8.21 (A10), U9.26 (A13), U10.21 (A10)
/A4: U2.14 (Q0), U7.2 (A12), U8.9 (A1), U9.2 (A12), U10.9 (A1)
/A5: U2.13 (Q1), U7.3 (A7), U8.8 (A2), U9.3 (A7), U10.8 (A2)
/A6: U2.12 (Q2), U7.4 (A6), U8.7 (A3), U9.4 (A6), U10.7 (A3)
/A7: U2.11 (Q3), U7.5 (A5), U8.6 (A4), U9.5 (A5), U10.6 (A4)
/A8: U3.14 (Q0), U7.21 (A10), U8.26 (A13), U9.21 (A10), U10.26 (A13)
/A9: U3.13 (Q1), U7.1 (A14), U8.10 (A0), U9.1 (A14), U10.10 (A0)
/A10: U6.6 (O2), U7.8 (A2), U8.3 (A7), U9.8 (A2), U10.3 (A7)
/A11: U6.16 (O6), U7.6 (A4), U8.5 (A5), U9.6 (A4), U10.5 (A5)
/A12: U6.12 (O4), U7.9 (A1), U8.2 (A12), U9.9 (A1), U10.2 (A12)
/A13: U6.9 (O3), U7.10 (A0), U8.1 (A14), U9.10 (A0), U10.1 (A14)
/A14: U6.15 (O5), U7.7 (A3), U8.4 (A6), U9.7 (A3), U10.4 (A6)
/A15: U5.1 (A0), U6.5 (O1)
/A16: U5.2 (A1), U6.2 (O0)
/A17: U5.3 (A2), U6.19 (O7)
/AD0: J1.6, U6.7 (D2), U7.16 (Q4), U8.19 (Q7), U9.19 (Q7), U10.12 (Q1)
/AD1: J1.5, U6.17 (D6), U7.15 (Q3), U8.11 (Q0), U9.11 (Q0), U10.11 (Q0)
/AD2: J1.8, U6.13 (D4), U7.17 (Q5), U8.18 (Q6), U9.12 (Q1), U10.19 (Q7)
/AD3: J1.7, U6.8 (D3), U7.11 (Q0), U8.12 (Q1), U9.15 (Q3), U10.15 (Q3)
/AD4: J1.10, U6.14 (D5), U7.18 (Q6), U8.17 (Q5), U9.18 (Q6), U10.13 (Q2)
/AD5: J1.9, U6.4 (D1), U7.12 (Q1), U8.13 (Q2), U9.16 (Q4), U10.16 (Q4)
/AD6: J1.12, U6.3 (D0), U7.13 (Q2), U8.15 (Q3), U9.17 (Q5), U10.17 (Q5)
/AD7: J1.11, U6.18 (D7), U7.19 (Q7), U8.16 (Q4), U9.13 (Q2), U10.18 (Q6)
/BATT+: BT1.1 (+), D2.2 (A)
/BUS_A8: J1.14, U4.1 (A0)
/BUS_A9: J1.13, U4.2 (A1)
/CARRY0: U1.15 (TC), U2.7 (CEP), U2.10 (CET)
/CARRY1: U2.15 (TC), U3.7 (CEP), U3.10 (CET)
/RAMRST: D3.1 (K), J1.38
/SLEEP: D3.2 (A), R3.2, U5.5 (E2)
/~BLOCK: U1.1 (~MR), U2.1 (~MR), U3.1 (~MR), U4.14 (O1), U6.11 (Cp)
/~BYTE: U1.2 (CP), U2.2 (CP), U3.2 (CP), U4.12 (O3), U5.4 (E1)
/~CS0: U5.15 (O0), U7.20 (~CS)
/~CS1: U5.14 (O1), U8.20 (~CS)
/~CS2: U5.13 (O2), U9.20 (~CS)
/~CS3: U5.12 (O3), U10.20 (~CS)
/~CS4: TP4.1, U5.11 (O4)
/~CS5: TP2.1, U5.10 (O5)
/~CS6: TP3.1, U5.9 (O6)
/~CS7: TP1.1, U5.7 (O7)
/~RD: J1.24, U7.22 (~OE), U8.22 (~OE), U9.22 (~OE), U10.22 (~OE)
/~WR: J1.23, U7.27 (~WE), U8.27 (~WE), U9.27 (~WE), U10.27 (~WE)
/~Y0: J1.29, U4.5 (E2)
GND: BT1.2 (-), C1.2, C2.2, C3.2, C4.2, C5.2, C6.2, C7.2, J1.3, J1.4, J1.21, J1.22, J1.35, J1.36, R2.2, U1.3 (D0), U1.4 (D1), U1.5 (D2), U1.6 (D3), U1.8 (GND), U2.3 (D0), U2.4 (D1), U2.5 (D2), U2.6 (D3), U2.8 (GND), U3.3 (D0), U3.4 (D1), U3.5 (D2), U3.6 (D3), U3.8 (GND), U4.3 (A2), U4.4 (E1), U4.8 (GND), U5.8 (GND), U6.1 (OE), U6.10 (GND), U7.14 (GND), U8.14 (GND), U9.14 (GND), U10.14 (GND); also elsewhere on the board
VBUS: C5.1, C6.1, C7.1, D1.2 (A), J1.1, J1.2, R2.1, U1.7 (CEP), U1.9 (~PE), U1.10 (CET), U1.16 (VCC), U2.9 (~PE), U2.16 (VCC), U3.9 (~PE), U3.16 (VCC), U4.16 (VCC), U5.6 (E3), U6.20 (VCC)
VMEM: C1.1, C2.1, C3.1, C4.1, D1.1 (K), D2.1 (K), R3.1, U5.16 (VCC), U7.28 (VCC), U8.28 (VCC), U9.28 (VCC), U10.28 (VCC)

Notes on the sheet:
SYSTEM BUS connection shown using the standard pin numbering for the connector, not the odd<>even swapped numbering from the TANDY Model 102 & 200 manuals.
TANDY 102/200 SYSTEM BUS
+5VDC
A15
INTR
A14
ALE
~{INTA}
CLK
GND
IO/~{M}
D3: Mod found on one of two original DATAPACs. Prevent host battery drain via RAMRST through R3 to VMEM?
VDD
A10
RESET
+3VDC
While ~{BLOCK} is low, A0-A9 are set to 0, AD0-AD7 are copied to A10-A17. While ~{BLOCK} is high, A10-A17 are latched. While ~{BYTE} is low, SRAM is enabled. When ~{BYTE} goes from low to high, A0-A9 are incremented by 1. While ~{BYTE} is high, SRAM is disabled. A0-A9 = 1024 bytes per block A10-A17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
A11
128K Install 4 SRAM in U7-U10. 256K Install 128K, then piggyback another 4 SRAM on top of U7-U10, with their pin 20 bent out and connected to TP1-TP4.
A13
A12

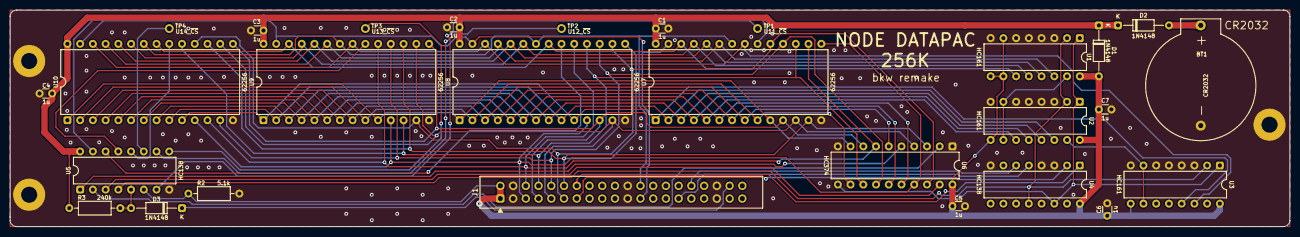
[picture p151: board NODE_DATAPAC_256K_bkw.kicad_pcb from above]

Board: 2 copper layers, 255.3 x 43.2 mm, 31 parts (0 on the bottom side), 50 nets.

Other parts of the board:
H1, H2, H3: MountHole; MountingHole_3.2mm_M3_Pad

Their connections:
GND: H1.1, H2.1, H3.1; also elsewhere on the board
