bkw777/NODE_DATAPAC/PCB/MiniNDP_512.kicad_pcb

## KiCad design PCB/MiniNDP_512.kicad_pcb (2024-06-13)

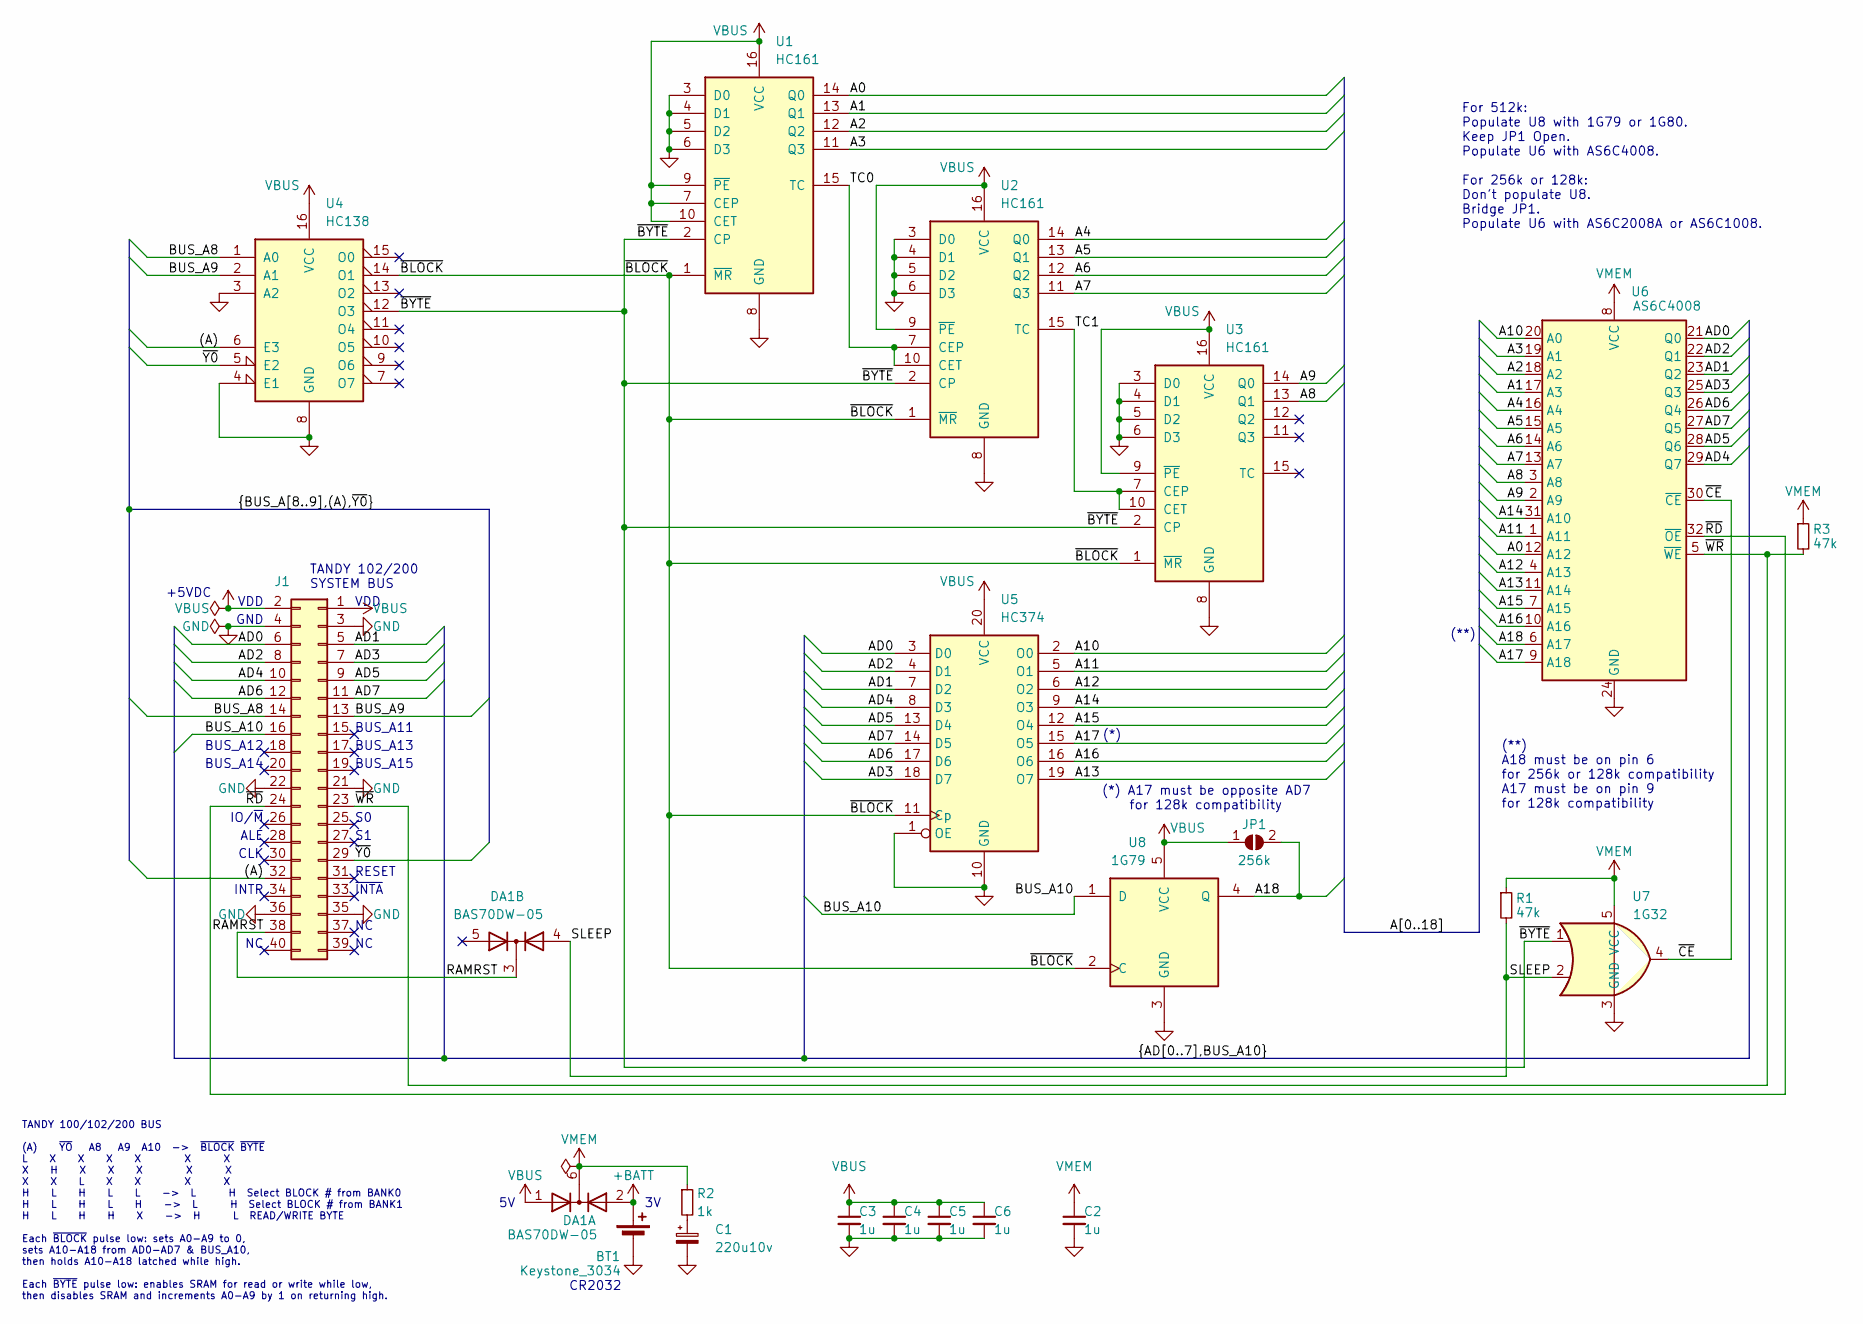
[picture p152: schematic MiniNDP_512.kicad_sch, MiniNDP 512]

Parts:
BT1: Keystone_3034; Keystone_3028_3034
C1: 220u10v; CP_6032
C2, C3, C4, C5, C6: 1u; C_0805
DA1: BAS70DW-05; SOT-363_SC-70-6_symmetric
J1: Conn_02x20_Odd_Even; IDC-Header_2x20_P2.54mm_Vertical
JP1: 256k; SolderJumper-2_Open 0.65mm
R1, R3: 47k; R_0805
R2: 1k; R_0805
U1, U2, U3: HC161; TSSOP-16
U4: HC138; TSSOP-16
U5: HC374; TSSOP-20
U6: AS6C4008; TSOP32-dual
U7: 1G32; SOT-353_SC-70-5
U8: 1G79; SOT-353_SC-70-5

Connections:
+BATT: BT1.1 (+), DA1.2 (A)
/(A): J1.32, U4.6 (E3)
/A0: U1.14 (Q0), U6.12 (A12)
/A1: U1.13 (Q1), U6.17 (A3)
/A2: U1.12 (Q2), U6.18 (A2)
/A3: U1.11 (Q3), U6.19 (A1)
/A4: U2.14 (Q0), U6.16 (A4)
/A5: U2.13 (Q1), U6.15 (A5)
/A6: U2.12 (Q2), U6.14 (A6)
/A7: U2.11 (Q3), U6.13 (A7)
/A8: U3.13 (Q1), U6.3 (A8)
/A9: U3.14 (Q0), U6.2 (A9)
/A10: U5.2 (O0), U6.20 (A0)
/A11: U5.5 (O1), U6.1 (A11)
/A12: U5.6 (O2), U6.4 (A13)
/A13: U5.19 (O7), U6.11 (A14)
/A14: U5.9 (O3), U6.31 (A10)
/A15: U5.12 (O4), U6.7 (A15)
/A16: U5.16 (O6), U6.10 (A16)
/A17: U5.15 (O5), U6.9 (A18)
/A18: JP1.2 (B), U6.6 (A17), U8.4 (Q)
/AD0: J1.6, U5.3 (D0), U6.21 (Q0)
/AD1: J1.5, U5.7 (D2), U6.23 (Q2)
/AD2: J1.8, U5.4 (D1), U6.22 (Q1)
/AD3: J1.7, U5.18 (D7), U6.25 (Q3)
/AD4: J1.10, U5.8 (D3), U6.29 (Q7)
/AD5: J1.9, U5.13 (D4), U6.28 (Q6)
/AD6: J1.12, U5.17 (D6), U6.26 (Q4)
/AD7: J1.11, U5.14 (D5), U6.27 (Q5)
/BUS_A8: J1.14, U4.1 (A0)
/BUS_A9: J1.13, U4.2 (A1)
/BUS_A10: J1.16, U8.1 (D)
/RAMRST: DA1.3 (K), J1.38
/SLEEP: DA1.4 (A), R1.2, U7.2
/TC0: U1.15 (TC), U2.7 (CEP), U2.10 (CET)
/TC1: U2.15 (TC), U3.7 (CEP), U3.10 (CET)
/~BLOCK: U1.1 (~MR), U2.1 (~MR), U3.1 (~MR), U4.14 (O1), U5.11 (Cp), U8.2 (C)
/~BYTE: U1.2 (CP), U2.2 (CP), U3.2 (CP), U4.12 (O3), U7.1
/~CE: U6.30 (~CE), U7.4
/~RD: J1.24, U6.32 (~OE)
/~WR: J1.23, R3.2, U6.5 (~WE)
/~Y0: J1.29, U4.5 (E2)
GND: BT1.2 (-), C1.2, C2.2, C3.2, C4.2, C5.2, C6.2, J1.3, J1.4, J1.21, J1.22, J1.35, J1.36, U1.3 (D0), U1.4 (D1), U1.5 (D2), U1.6 (D3), U1.8 (GND), U2.3 (D0), U2.4 (D1), U2.5 (D2), U2.6 (D3), U2.8 (GND), U3.3 (D0), U3.4 (D1), U3.5 (D2), U3.6 (D3), U3.8 (GND), U4.3 (A2), U4.4 (E1), U4.8 (GND), U5.1 (OE), U5.10 (GND), U6.24 (GND), U7.3 (GND), U8.3 (GND)
unnamed: C1.1, R2.2
VBUS: C3.1, C4.1, C5.1, C6.1, DA1.1 (A), J1.1, J1.2, JP1.1 (A), U1.7 (CEP), U1.9 (~PE), U1.10 (CET), U1.16 (VCC), U2.9 (~PE), U2.16 (VCC), U3.9 (~PE), U3.16 (VCC), U4.16 (VCC), U5.20 (VCC), U8.5 (VCC)
VMEM: C2.1, DA1.6 (K), R1.1, R2.1, R3.1, U6.8 (VCC), U7.5 (VCC)

Notes on the sheet:
TANDY 102/200 SYSTEM BUS
+5VDC
BUS_A15
INTR
BUS_A14
ALE
~{INTA}
CLK
(**) A18 must be on pin 6 for 256k or 128k compatibility A17 must be on pin 9 for 128k compatibility
GND
For 512k: Populate U8 with 1G79 or 1G80. Keep JP1 Open. Populate U6 with AS6C4008. For 256k or 128k: Don't populate U8. Bridge JP1. Populate U6 with AS6C2008A or AS6C1008.
IO/~{M}
CR2032
VDD
TANDY 100/102/200 BUS (A) ~{YO} A8 A9 A10 -> ~{BLOCK} ~{BYTE} L X X X X X X X H X X X X X X X L X X X X H L H L L -> L H Select BLOCK # from BANK0 H L H L H -> L H Select BLOCK # from BANK1 H L H H X -> H L READ/WRITE BYTE Each ~{BLOCK} pulse low: sets A0-A9 to 0, sets A10-A18 from AD0-AD7 & BUS_A1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
RESET
(*) A17 must be opposite AD7 for 128k compatibility
(**)
BUS_A11
BUS_A13
(*)
BUS_A12

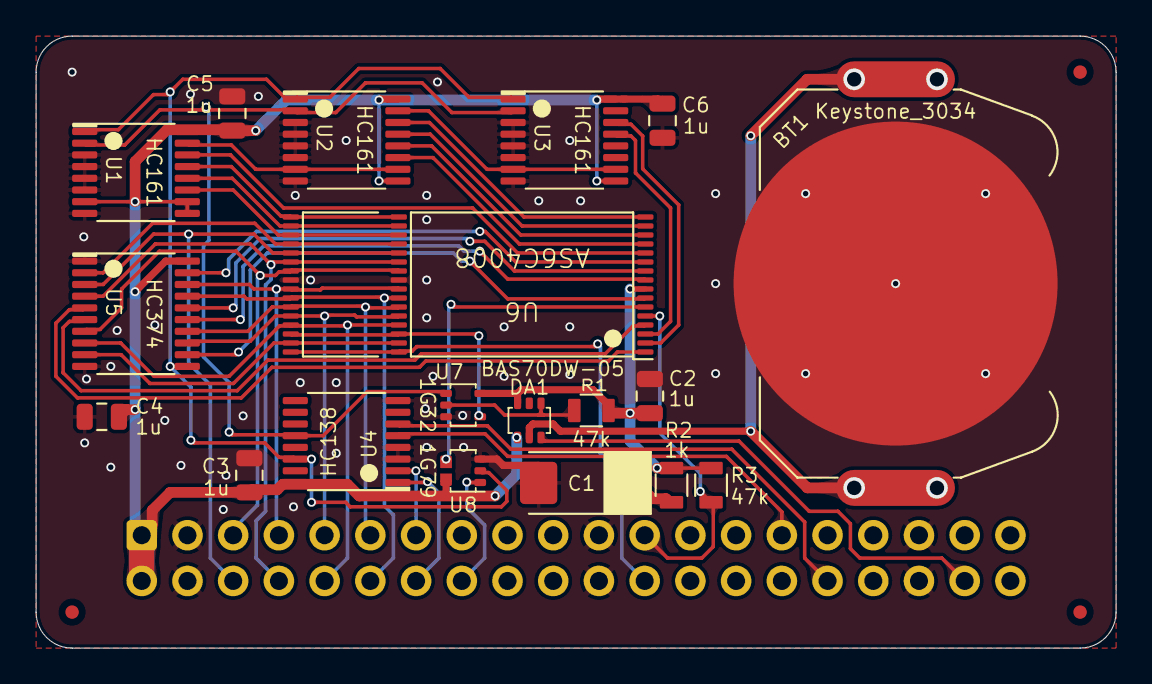
[picture p153: board MiniNDP_512.kicad_pcb from above]

Board: 2 copper layers, 60.0 x 34.0 mm, 25 parts (1 on the bottom side), 46 nets.

Other parts of the board:
ENCLOSURE: MiniNDP_Cover
F3, F3#2, F3#3: Fiducial_0.75_1.5
