bkw777/NODE_DATAPAC/PCB/MiniNDP_1M_B.kicad_pcb

## KiCad design PCB/MiniNDP_1M_B.kicad_pcb (2024-05-28)

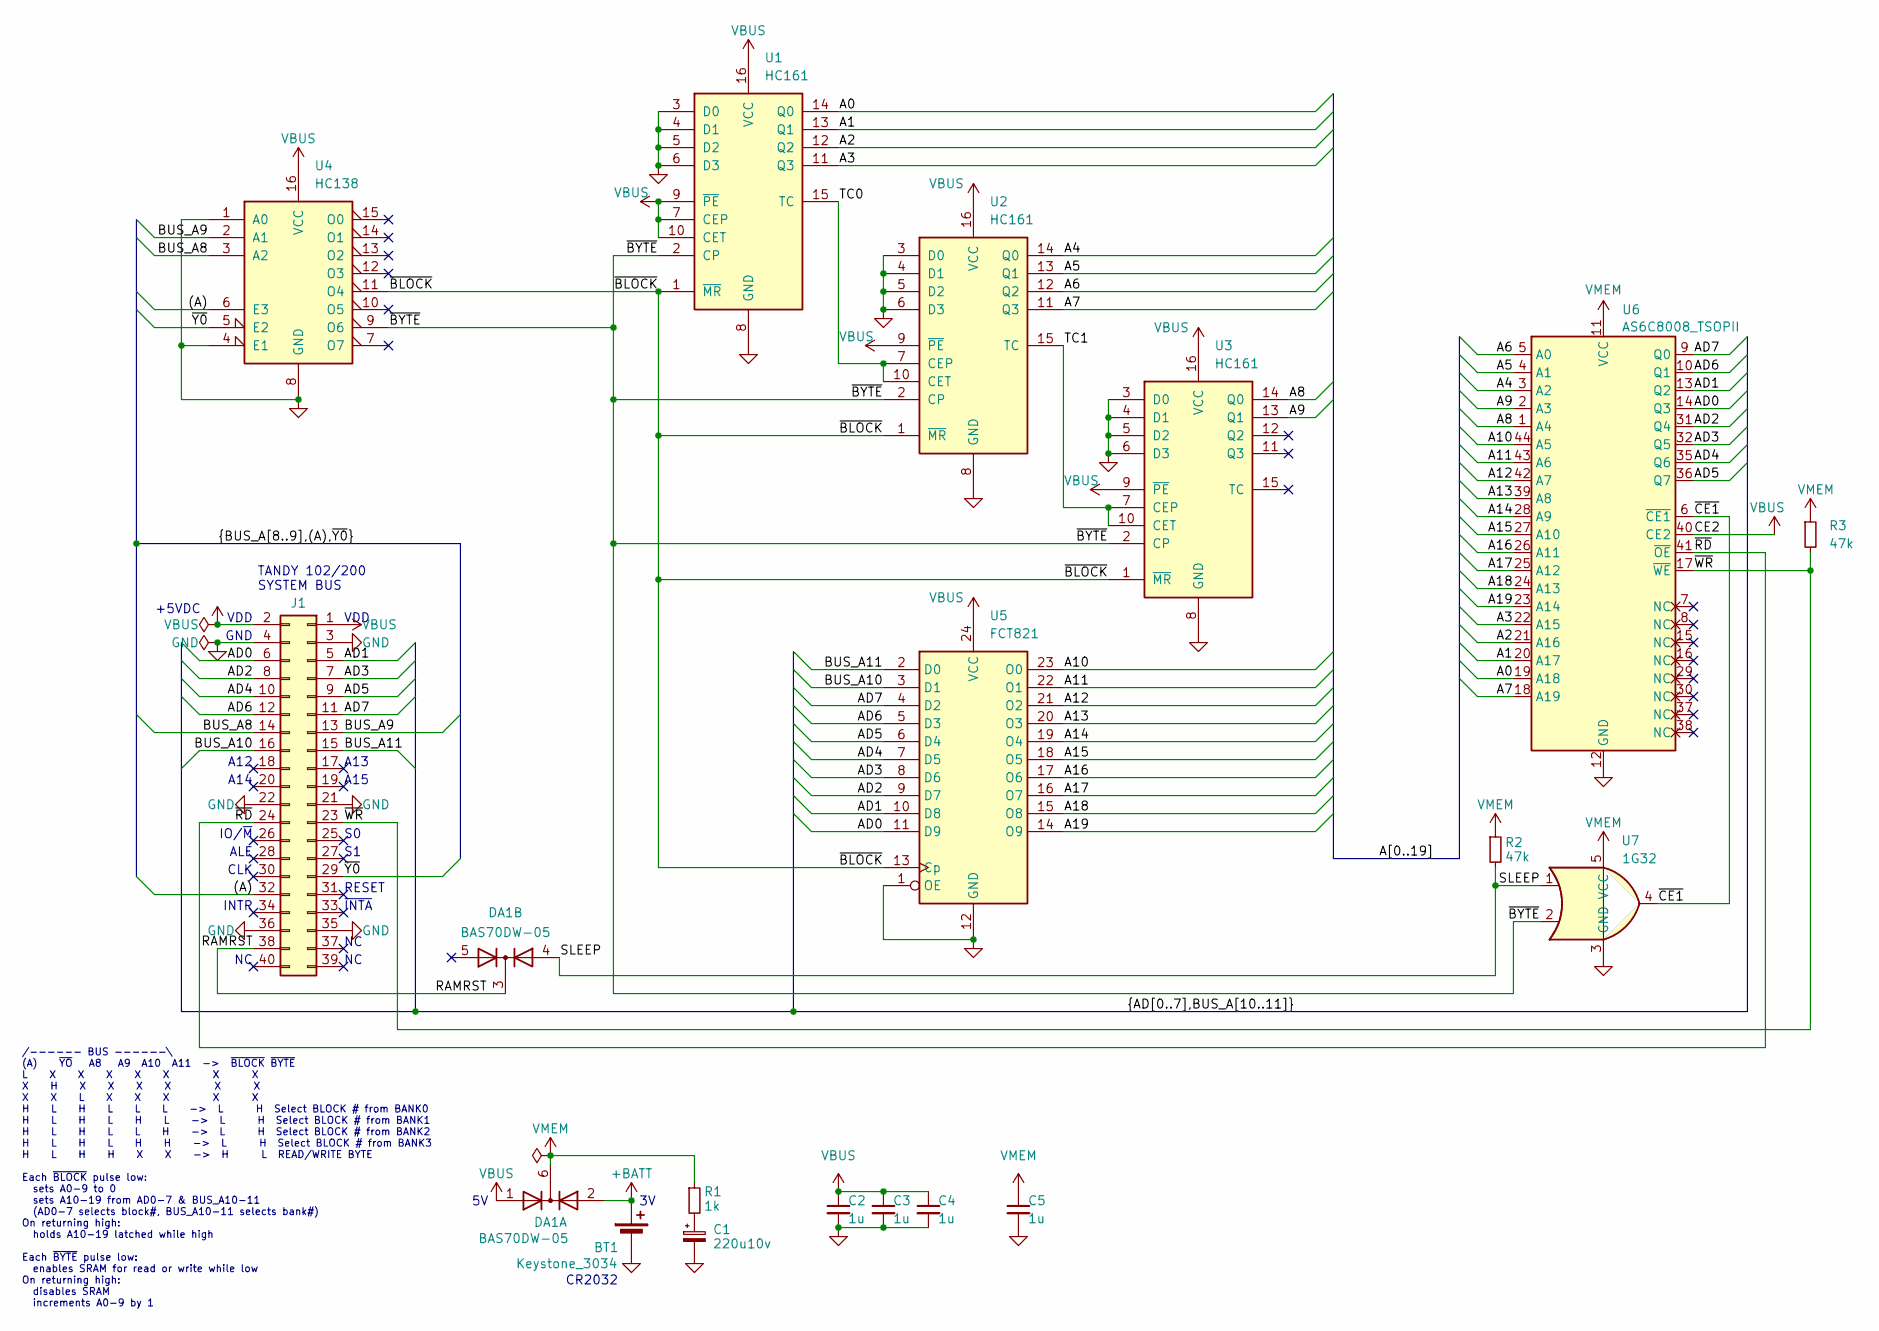
[picture p154: schematic MiniNDP_1M_B.kicad_sch, MiniNDP 1M]

Parts:
BT1: Keystone_3034; Keystone_3028_3034
C1: 220u10v; CP_6032
C2, C3, C4, C5: 1u; C_0805
DA1: BAS70DW-05; SOT-363_SC-70-6_symmetric
J1: Conn_02x20_Odd_Even; IDC-Header_2x20_P2.54mm_Vertical
R1: 1k; R_0805
R2, R3: 47k; R_0805
U1, U2, U3: HC161; TSSOP-16
U4: HC138; TSSOP-16
U5: FCT821; SOIC-24
U6: AS6C8008_TSOPII; TSOP-II-44
U7: 1G32; SOT-353_SC-70-5

Connections:
+BATT: BT1.1 (+), DA1.2 (A)
/(A): J1.32, U4.6 (E3)
/A0: U1.14 (Q0), U6.19 (A18)
/A1: U1.13 (Q1), U6.20 (A17)
/A2: U1.12 (Q2), U6.21 (A16)
/A3: U1.11 (Q3), U6.22 (A15)
/A4: U2.14 (Q0), U6.3 (A2)
/A5: U2.13 (Q1), U6.4 (A1)
/A6: U2.12 (Q2), U6.5 (A0)
/A7: U2.11 (Q3), U6.18 (A19)
/A8: U3.14 (Q0), U6.1 (A4)
/A9: U3.13 (Q1), U6.2 (A3)
/A10: U5.23 (O0), U6.44 (A5)
/A11: U5.22 (O1), U6.43 (A6)
/A12: U5.21 (O2), U6.42 (A7)
/A13: U5.20 (O3), U6.39 (A8)
/A14: U5.19 (O4), U6.28 (A9)
/A15: U5.18 (O5), U6.27 (A10)
/A16: U5.17 (O6), U6.26 (A11)
/A17: U5.16 (O7), U6.25 (A12)
/A18: U5.15 (O8), U6.24 (A13)
/A19: U5.14 (O9), U6.23 (A14)
/AD0: J1.6, U5.11 (D9), U6.14 (Q3)
/AD1: J1.5, U5.10 (D8), U6.13 (Q2)
/AD2: J1.8, U5.9 (D7), U6.31 (Q4)
/AD3: J1.7, U5.8 (D6), U6.32 (Q5)
/AD4: J1.10, U5.7 (D5), U6.35 (Q6)
/AD5: J1.9, U5.6 (D4), U6.36 (Q7)
/AD6: J1.12, U5.5 (D3), U6.10 (Q1)
/AD7: J1.11, U5.4 (D2), U6.9 (Q0)
/BUS_A8: J1.14, U4.3 (A2)
/BUS_A9: J1.13, U4.2 (A1)
/BUS_A10: J1.16, U5.3 (D1)
/BUS_A11: J1.15, U5.2 (D0)
/RAMRST: DA1.3 (K), J1.38
/SLEEP: DA1.4 (A), R2.2, U7.1
/TC0: U1.15 (TC), U2.7 (CEP), U2.10 (CET)
/TC1: U2.15 (TC), U3.7 (CEP), U3.10 (CET)
/~BLOCK: U1.1 (~MR), U2.1 (~MR), U3.1 (~MR), U4.11 (O4), U5.13 (Cp)
/~BYTE: U1.2 (CP), U2.2 (CP), U3.2 (CP), U4.9 (O6), U7.2
/~CE1: U6.6 (~CE1), U7.4
/~RD: J1.24, U6.41 (~OE)
/~WR: J1.23, R3.2, U6.17 (~WE)
/~Y0: J1.29, U4.5 (E2)
GND: BT1.2 (-), C1.2, C2.2, C3.2, C4.2, C5.2, J1.3, J1.4, J1.21, J1.22, J1.35, J1.36, U1.3 (D0), U1.4 (D1), U1.5 (D2), U1.6 (D3), U1.8 (GND), U2.3 (D0), U2.4 (D1), U2.5 (D2), U2.6 (D3), U2.8 (GND), U3.3 (D0), U3.4 (D1), U3.5 (D2), U3.6 (D3), U3.8 (GND), U4.1 (A0), U4.4 (E1), U4.8 (GND), U5.1 (OE), U5.12 (GND), U6.12 (GND), U6.34 (GND), U7.3 (GND)
unnamed: C1.1, R1.2
VBUS: C2.1, C3.1, C4.1, DA1.1 (A), J1.1, J1.2, U1.7 (CEP), U1.9 (~PE), U1.10 (CET), U1.16 (VCC), U2.9 (~PE), U2.16 (VCC), U3.9 (~PE), U3.16 (VCC), U4.16 (VCC), U5.24 (VCC), U6.40 (CE2)
VMEM: C5.1, DA1.6 (K), R1.1, R2.1, R3.1, U6.11 (VCC), U6.33 (VCC), U7.5 (VCC)

Notes on the sheet:
TANDY 102/200 SYSTEM BUS
+5VDC
A15
CR2032
INTR
A14
ALE
~{INTA}
CLK
GND
IO/~{M}
VDD
/------ BUS ------\ (A) ~{YO} A8 A9 A10 A11 -> ~{BLOCK} ~{BYTE} L X X X X X X X X H X X X X X X X X L X X X X X H L H L L L -> L H Select BLOCK # from BANK0 H L H L H L -> L H Select BLOCK # from BANK1 H L H L L H -> L H Select BLOCK # from BANK2 H L H L H H -> L H Select BLOCK # from BANK3 H L H H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
RESET
A13
A12

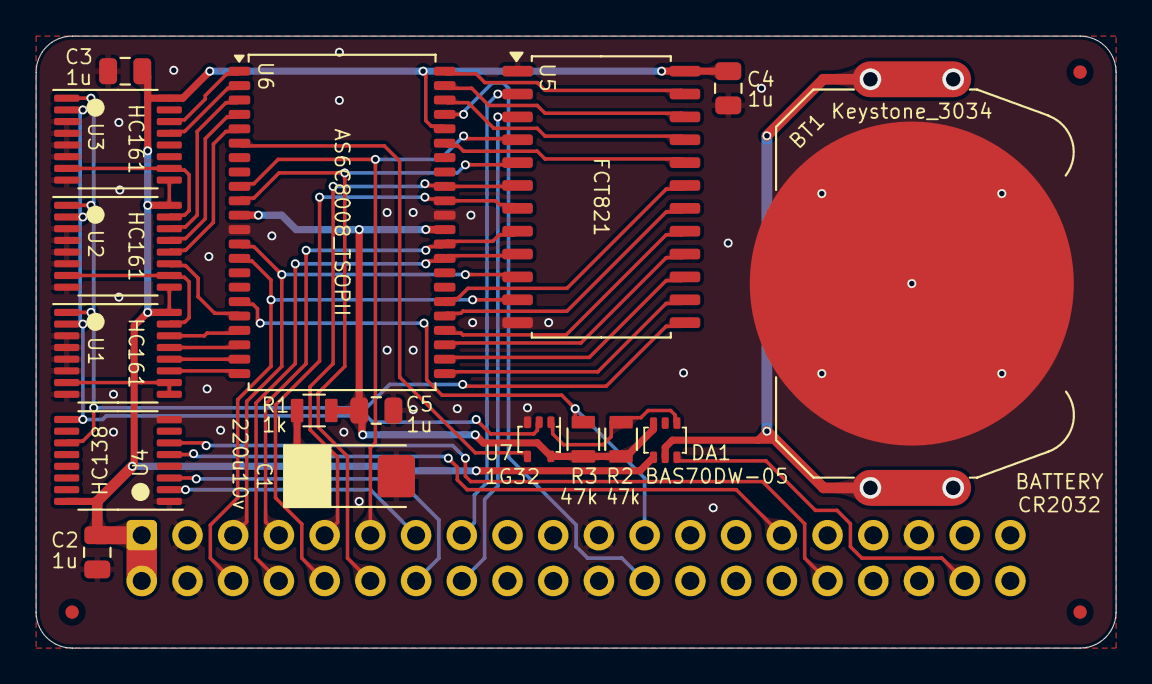
[picture p155: board MiniNDP_1M_B.kicad_pcb from above]

Board: 2 copper layers, 60.0 x 34.0 mm, 22 parts (1 on the bottom side), 48 nets.

Other parts of the board:
ENCLOSURE: MiniNDP_Cover
F2, F2#2, F3: Fiducial_0.75_1.5
