bkw777/NODE_DATAPAC/ref/MiniNDP_FDS_slip_cover.jpg

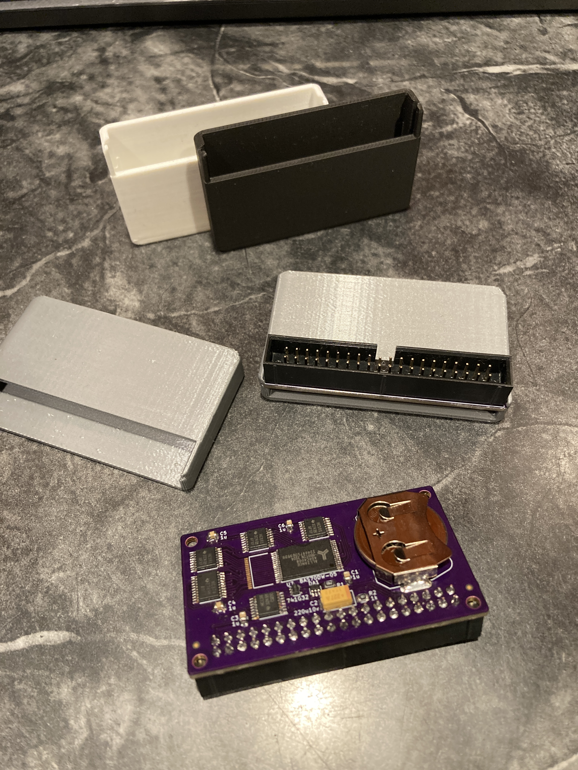
ref/MiniNDP_FDS_slip_cover.jpg
